s2311119/portable-game/portable-game-console/portable-game-console.ino

// main.ino
#include <SPI.h>
#include <SdFat.h>
#include "LGFX_RP2040_ILI9341.hpp"
#include <LGFX_TFT_eSPI.hpp>  // フォントを使う場合に必要な場合もあります
#include "bmp.h"

#include "pico/stdlib.h"
#include "pico/multicore.h"
#include "pico/time.h"
#include "hardware/gpio.h"

#include "pico/sync.h"
critical_section_t sdLock;

#define LGFX_USE_SD 1
#define H_TRANSPARENT 0xFFFF
#include <malloc.h>
// -------------------------
// 変更が必要なピン設定（回路依存）
// -------------------------
static const int SD_CS_PIN = 22;    // SD カード CS
static const int SD_MISO_PIN = 16;  // SD MISO（プルアップ必須）
static const int SD_SCK_PIN  = 18;
static const int SD_MOSI_PIN = 19;

static const int DAC_CS_PIN   = 17; // MCP4921 CS
static const int DAC_SCK_PIN  = 9;  // ソフトSPIクロック
static const int DAC_MOSI_PIN = 8;  // ソフトSPI MOSI

// -------------------------
// Map / Game / Graphic 等（省略せずそのまま）
// -------------------------
// ここは質問者が既に持っているゲームロジック部分をそのまま使います。
// （読みやすさのため必要最小限のみ再掲します）
// main.ino

#include <vector>      // std::vector を使うために必要
#include <algorithm>   // std::min, std::max を使うために必要

//-----------------------------
/*
ストライカー系: 39->44->49->{54, 55} ->{{61, 62}, {63, 64}}
ガーディアン系: 40->45->50->{56, 57} ->{{65, 66}, {67. 68}}
クリッパー系: 41->46->51->58 ->{69, 70}
メンダ―系: 42->47->52->59 ->{71, 72}
ジャマー系: 43->48->53->60->{73, 74}
*/
//-----------------------------

// グローバル（core0 から参照するけど SD 操作は core1 のみ）
enum EventType {
  EVENT_NONE,
  EVENT_TREASURE_BOX,
  EVENT_STAIR_UP,
  EVENT_STAIR_DOWN,
  EVENT_AUTOMATON,
  EVENT_INN,     // ★追加
  EVENT_SHOP,    // ★追加
  EVENT_STORAGE,  // ★追加
  EVENT_BOSS_BATTLE
};

enum GameState {
  STATE_GAME,
  STATE_MENU, 
  STATE_BATTLE,
  STATE_EVENT,
  STATE_GAME_OVER
};
#include <malloc.h> // これが必要です

class MemoryMonitor {
private:
  unsigned long lastCheckTime = 0;
  const unsigned long INTERVAL = 10000; // 10秒 (10000ms)

public:
  void update() {
    unsigned long now = millis();
    if (now - lastCheckTime >= INTERVAL) {
      lastCheckTime = now;
      printInfo();
    }
  }

  void printInfo() {
    struct mallinfo m = mallinfo();
    
    // RP2040のRAMは約264KBですが、プログラム領域などを除いた
    // ヒープとして使える領域の統計を表示します。
    
    Serial.println("=== Memory Status (10s) ===");
    Serial.printf("Used (使用中): %d bytes (%.2f KB)\n", m.uordblks, m.uordblks / 1024.0);
    Serial.printf("Free (空き)  : %d bytes (%.2f KB)\n", m.fordblks, m.fordblks / 1024.0);
    
    // メモリ断片化の目安（空きがあるのに大きい確保ができない原因）
    // これが小さいと、大きな連続したメモリ(画像など)が確保できません
    // Serial.printf("Max Free Block: %d bytes\n", m.mxordblk); // (環境によっては0になる場合あり)
    
    Serial.println("===========================");
  }
};

class Map {
public:
  int MAP_WIDTH;
  int MAP_HEIGHT;
  int automatonWhoId;
  int currentFloor = 1;
  // マップの寸法（コンストラクタで決定）  
  static const int TILE_SIZE = 32;
  static const int TILE_GRASS = 0;
  static const int TILE_WALL  = 1;
  static const int TILE_STAIR_UP = 2;
  static const int TILE_STAIR_DOWN = 3;
  static const int TILE_BOX_CLOSE = 4;
  static const int TILE_BOX_OPEN = 5;
  static const int TILE_AUTOMATON = 6;
  static const int TILE_INN = 7;     // 宿屋
  static const int TILE_SHOP = 8;    // 店
  static const int TILE_STORAGE = 9; // 預かり所
  static const int TILE_BOSS = 99;//ボス
  // マップデータを保持する動的配列
  std::vector<uint8_t> mapData;

  enum MapType {
    TYPE_MAZE,
    TYPE_DUNGEON,
    TYPE_TOWN,
    TYPE_BOSS_ROOM
  };
  MapType currentType;
  bool isTown = false;
  // ★★★ 追加：部屋の矩形情報を保存する構造体 ★★★
  struct Room {
    int x, y, w, h;
  };

  struct ObjectPos {
    int x, y;
  };

  std::vector<ObjectPos> boxPositions; // 宝箱の位置リスト
  ObjectPos stairUpPos = {-1, -1};    // 上り階段の位置
  ObjectPos stairDownPos = {-1, -1};  // 下り階段の位置
  ObjectPos playerStartPos; //主人公の初期位置

  // ★★★ 修正後のコンストラクタ ★★★
  Map(int max_w, int max_h, MapType type)
  {
    // 初期化リスト (:) ではなく、ここで代入する
    currentType = type;
    /*MAP_WIDTH = ((type != TYPE_MAZE && type != TYPE_DUNGEON) ? random(4, max_w / 2) * 2 + 1 : random(15, max_w / 2) * 2 + 1);
    MAP_HEIGHT = ((type != TYPE_MAZE && type != TYPE_DUNGEON) ? random(4, max_h / 2) * 2 + 1 : random(15, max_h / 2) * 2 + 1);*/
    if (type == TYPE_TOWN) {
      // 集落: 床5x5 + 周囲の壁2 = 7x7
      MAP_WIDTH = 8;
      MAP_HEIGHT = 8;
    } 
    else if (type == TYPE_BOSS_ROOM) {
      // ボス部屋: 床7x7 + 周囲の壁2 = 9x9
      MAP_WIDTH = 9;
      MAP_HEIGHT = 9;
    }
    else {
      // ダンジョン: ランダム (奇数になるように調整)
      // ※ max_w/h が渡されていますが、最低サイズを下回らないように注意
      MAP_WIDTH = random(15, max_w / 2) * 2 + 1;
      MAP_HEIGHT = random(15, max_h / 2) * 2 + 1;
    }
    mapData.assign(MAP_WIDTH * MAP_HEIGHT, TILE_WALL);
    generateMazeAndRooms(type);
    placeObjects();
  }
  int getMAP_WIDTH(){
    return MAP_WIDTH;
  }
  int getMAP_HEIGHT(){
    return MAP_HEIGHT;
  }
  void regenerate(int max_w, int max_h, MapType type){
    // public側のMAP_WIDTH/HEIGHTを変更する
    currentType = type;
    
    isTown = false;
    if (type == TYPE_TOWN) {
      // 集落: 床5x5 + 周囲の壁2 = 7x7
      MAP_WIDTH = 8;
      MAP_HEIGHT = 8;
      isTown = true;
    } 
    else if (type == TYPE_BOSS_ROOM) {
      // ボス部屋: 床7x7 + 周囲の壁2 = 9x9
      MAP_WIDTH = 9;
      MAP_HEIGHT = 9;
    }
    else {
      // ダンジョン: ランダム (奇数になるように調整)
      // ※ max_w/h が渡されていますが、最低サイズを下回らないように注意
      MAP_WIDTH = random(15, max_w / 2) * 2 + 1;
      MAP_HEIGHT = random(15, max_h / 2) * 2 + 1;
    }
    mapData.assign(MAP_WIDTH * MAP_HEIGHT, TILE_WALL);
    if (type == TYPE_BOSS_ROOM) {
      // --- ボス部屋の描画 ---
      
      // 全体を床にする
      for (int i = 0; i < MAP_WIDTH * MAP_HEIGHT; i++) mapData[i] = TILE_GRASS;
      
      // 周囲を壁にする
      for (int x = 0; x < MAP_WIDTH; x++) { 
          mapData[x] = TILE_WALL; 
          mapData[(MAP_HEIGHT-1)*MAP_WIDTH + x] = TILE_WALL; 
      }
      for (int y = 0; y < MAP_HEIGHT; y++) { 
          mapData[y*MAP_WIDTH] = TILE_WALL; 
          mapData[y*MAP_WIDTH + (MAP_WIDTH-1)] = TILE_WALL; 
      }

      // 下り階段 (入り口)
      // 座標が範囲外にならないよう中央下付近に固定
      int stairX = MAP_WIDTH / 2;
      int stairY = MAP_HEIGHT - 3;
      mapData[stairY * MAP_WIDTH + stairX] = TILE_STAIR_DOWN;
      
      // プレイヤー開始位置
      playerStartPos = {stairX, stairY};

      // ★ボス配置 (部屋の中央奥)
      int bossX = MAP_WIDTH / 2;
      int bossY = 5;
      mapData[bossY * MAP_WIDTH + bossX] = TILE_BOSS;

      return; // ボス部屋生成完了
    }
    // メンバー変数を再利用して再生成
    generateMazeAndRooms(type);
    placeObjects();
  }
private:
  //int MAP_WIDTH;
  //int MAP_HEIGHT;
  std::vector<int> pathX, pathY;
  std::vector<int> dirs;
  std::vector<Room> placedRooms;
  std::vector<ObjectPos> grassTiles;
  void generateMazeAndRooms(MapType type) {
    if (type == TYPE_TOWN) {
      // 1. 全体を壁で初期化 (コンストラクタ等で既にされているが念のため)
      // mapData.assign(MAP_WIDTH * MAP_HEIGHT, TILE_WALL); 

      // 2. 中央に大きな広場(草)を作る
      int margin = 2; 
      // マップが小さすぎる場合の保護
      if (MAP_WIDTH <= margin * 2 || MAP_HEIGHT <= margin * 2) margin = 1;

      for(int y = margin; y < MAP_HEIGHT - margin; y++) {
        for(int x = margin; x < MAP_WIDTH - margin; x++) {
          mapData[y * MAP_WIDTH + x] = TILE_GRASS;
        }
      }
      // 集落生成はこれで終わり（階段などは placeObjects で）
      return; 
    }
    if (currentFloor >= 21 && random(100) < 5) { // 例: 5%の確率
      automatonWhoId = 75;
    } 
    else {
      // 通常の仲間
      const int basicAllies[] = {39, 40, 41, 42, 43};
      automatonWhoId = basicAllies[random(5)];
    }
    // --- 1. 穴掘り法 ---
    int startX = 1, startY = 1;
    
    // ★ メンバー変数をクリアして再利用 (new しない)
    pathX.clear(); pathY.clear();
    pathX.reserve(MAP_WIDTH * MAP_HEIGHT / 4);
    pathY.reserve(MAP_WIDTH * MAP_HEIGHT / 4);
    
    pathX.push_back(startX); pathY.push_back(startY);
    mapData[startY * MAP_WIDTH + startX] = TILE_GRASS;
    int dx[]={0,2,0,-2}, dy[]={-2,0,2,0};

    while(!pathX.empty()){
      int cx=pathX.back(), cy=pathY.back();
      
      dirs.clear(); // ★ メンバー変数を再利用
      dirs.reserve(4);
      
      for(int i=0;i<4;i++){
        int nx=cx+dx[i], ny=cy+dy[i];
        if(nx>0 && nx<MAP_WIDTH-1 && ny>0 && ny<MAP_HEIGHT-1 && mapData[ny * MAP_WIDTH + nx]==TILE_WALL) dirs.push_back(i);
      }
      if(!dirs.empty()){
        int dir = dirs[random((int)dirs.size())];
        int wallX = cx + dx[dir]/2, wallY = cy + dy[dir]/2;
        int nextX = cx + dx[dir], nextY = cy + dy[dir];
        mapData[wallY * MAP_WIDTH + wallX] = TILE_GRASS;
        mapData[nextY * MAP_WIDTH + nextX] = TILE_GRASS;
        pathX.push_back(nextX); pathY.push_back(nextY);
      } else {
        pathX.pop_back(); pathY.pop_back();
      }
    }

    // --- 2. rooms ---
    if(type == TYPE_DUNGEON) {
      int numRooms = random(0, 3);
      int minRoomSize = 3;
      int maxRoomSize = 8;

      placedRooms.clear(); // ★ メンバー変数を再利用
      placedRooms.reserve(numRooms);

      int maxAttempts = 100;

      for (int i = 0; i < numRooms; i++) {
        bool roomPlaced = false;
        for (int attempt = 0; attempt < maxAttempts; attempt++) {
          int w = random(minRoomSize, maxRoomSize + 1);
          int h = random(minRoomSize, maxRoomSize + 1);
          int x = random(1, MAP_WIDTH - w - 2);
          int y = random(1, MAP_HEIGHT - h - 2);
          Room newRoom = {x, y, w, h};
          bool overlaps = false;
          for (const auto& existingRoom : placedRooms) {
            if (newRoom.x < existingRoom.x + existingRoom.w &&
                newRoom.x + newRoom.w > existingRoom.x &&
                newRoom.y < existingRoom.y + existingRoom.h &&
                newRoom.y + newRoom.h > existingRoom.y) {
              overlaps = true; break;
            }
          }
          if (!overlaps) {
            carveRoom(newRoom.x, newRoom.y, newRoom.x + newRoom.w, newRoom.y + newRoom.h);
            placedRooms.push_back(newRoom);
            roomPlaced = true;
            break;
          }
        }
      }
    }
  }

  // (generateDungeon のヘルパー関数) 部屋を掘る
  void carveRoom(int x1, int y1, int x2, int y2) {
    for (int y = y1; y < y2; y++) {
      for (int x = x1; x < x2; x++) {
        if (x > 0 && x < MAP_WIDTH - 1 && y > 0 && y < MAP_HEIGHT - 1) {
          mapData[y * MAP_WIDTH + x] = TILE_GRASS;
        }
      }
    }
  }

  void placeObjects() {
    boxPositions.clear();
    stairUpPos = {-1, -1};
    stairDownPos = {-1, -1};
    playerStartPos = {1, 1};

    grassTiles.clear(); // ★ メンバー変数を再利用
    grassTiles.reserve((MAP_WIDTH-2) * (MAP_HEIGHT-2) / 2);
    for (int y = 1; y < MAP_HEIGHT - 1; ++y) {
      for (int x = 1; x < MAP_WIDTH - 1; ++x) {
        if (mapData[y * MAP_WIDTH + x] == TILE_GRASS) grassTiles.push_back({x,y});
      }
    }
    if (grassTiles.empty()) return;
    int idx;
    
    if (currentType == TYPE_TOWN) {
      // 1. 上り階段
      idx = random((int)grassTiles.size());
      stairUpPos = grassTiles[idx];
      mapData[stairUpPos.y * MAP_WIDTH + stairUpPos.x] = TILE_STAIR_UP;
      grassTiles[idx] = grassTiles.back(); grassTiles.pop_back();

      // 2. 下り階段 (1階以外)
      if (currentFloor > 1 && !grassTiles.empty()) {
        idx = random((int)grassTiles.size());
        stairDownPos = grassTiles[idx];
        mapData[stairDownPos.y * MAP_WIDTH + stairDownPos.x] = TILE_STAIR_DOWN;
        grassTiles[idx] = grassTiles.back(); grassTiles.pop_back();
      }
      if (currentFloor > 1){
        playerStartPos = stairDownPos;
      }else{
        playerStartPos = grassTiles[random((int)grassTiles.size())];
      }
      // ★★★ 3. 施設の配置 ★★★
      if (!grassTiles.empty()) { // 宿屋
        idx = random((int)grassTiles.size());
        ObjectPos pos = grassTiles[idx];
        mapData[pos.y * MAP_WIDTH + pos.x] = TILE_INN;
        grassTiles[idx] = grassTiles.back(); grassTiles.pop_back();
      }
      if (!grassTiles.empty()) { // 店
        idx = random((int)grassTiles.size());
        ObjectPos pos = grassTiles[idx];
        mapData[pos.y * MAP_WIDTH + pos.x] = TILE_SHOP;
        grassTiles[idx] = grassTiles.back(); grassTiles.pop_back();
      }
      if (!grassTiles.empty()) { // 預かり所
        idx = random((int)grassTiles.size());
        ObjectPos pos = grassTiles[idx];
        mapData[pos.y * MAP_WIDTH + pos.x] = TILE_STORAGE;
        grassTiles[idx] = grassTiles.back(); grassTiles.pop_back();
      }  
      return; 
    }

    // pick using swap-pop to avoid erase shift
    idx = random((int)grassTiles.size());
    stairDownPos = grassTiles[idx];
    playerStartPos = stairDownPos;
    mapData[stairDownPos.y * MAP_WIDTH + stairDownPos.x] = TILE_STAIR_DOWN;
    grassTiles[idx] = grassTiles.back();
    grassTiles.pop_back();

    idx = random((int)grassTiles.size());
    stairUpPos = grassTiles[idx];
    mapData[stairUpPos.y * MAP_WIDTH + stairUpPos.x] = TILE_STAIR_UP;
    grassTiles[idx] = grassTiles.back();
    grassTiles.pop_back();

    if (!grassTiles.empty()) {
      idx = random((int)grassTiles.size());
      ObjectPos allyPos = grassTiles[idx];
      // ★ TODO: 今は 39 で固定。将来的にはフロア番号で who ID を変える
      // (mapData は who ID を保持できないので、別の変数に持つ)
      mapData[allyPos.y * MAP_WIDTH + allyPos.x] = TILE_AUTOMATON; 
      grassTiles[idx] = grassTiles.back();
      grassTiles.pop_back();
    }

    int maxBoxes = std::max(0, (int)grassTiles.size() / 5);
    int numBoxes = 0;
    if (maxBoxes > 0) numBoxes = random(1, std::min(maxBoxes, 10) + 1);
    for (int i = 0; i < numBoxes; ++i) {
      if (grassTiles.empty()) break;
      int j = random((int)grassTiles.size());
      ObjectPos boxPos = grassTiles[j];
      mapData[boxPos.y * MAP_WIDTH + boxPos.x] = TILE_BOX_CLOSE;
      boxPositions.push_back(boxPos);
      grassTiles[j] = grassTiles.back();
      grassTiles.pop_back();
    }
  }

  // ★★★ 追加: 迷路生成後に宝箱と階段を配置する関数 ★★★
  
};

class Item {
public:
  enum ItemType {
    ITEM_CONSUMABLE, // 消費アイテム (回復薬など)
    ITEM_WEAPON,     // 武器
    ITEM_ARMOR,      // 防具
    ITEM_ACCESSORY,  // アクセサリー
    ITEM_MATERIAL,   // 素材 (換金用)
    ITEM_IMPORTANT   // 大事なもの
  };
  ItemType type; // ★ 追加: 種類
  int value;     // ★ 追加: 威力 (武器ならATK、防具ならDEF、薬なら回復量)
  int price;     // ★ 追加: 買値 (売値はこの半額にするのが一般的)
  int id;
  const char* name;

  // コンストラクタ
  Item(int _id = 0, const char* _name = "", ItemType _type = ITEM_MATERIAL, int _value = 0, int _price = 0) {
    id = _id;
    name = _name;
    type = _type;
    value = _value;
    price = _price;
  }
};

class Skill {
public:
  int id;
  const char* name;
  int tpCost; // ★消費TP (ゼンマイ)
  int power;  // ★技の威力 (Senseステータスで計算)
  enum class StatDependence {
    NONE, // 依存なし (固定値など)
    ATK,  // 物理 (Attack vs Defense)
    SEN   // 魔法/技術 (Sense vs Sense)
  };
  // main.ino (Skill クラスのコンストラクタ 322行目あたり)

  enum class EffectType {
    NONE,             // 効果なし
    DAMAGE,           // 物理・属性ダメージ (powerを参照)
    HEAL,             // HP回復 (powerを参照)
    CURE_STATUS,      // 状態異常の治療 (例: キュア)
    BUFF,             // 強化 (例: パワーチャージ, クイックステップ)
    DEBUFF,           // 弱体化 (例: スロウ, パワーダウン)
    REVIVE,           // 蘇生 (例: リザレクション)
    MULTI_HIT_DAMAGE, // 多段ヒット (例: ツインエッジ)
    SPECIAL           // その他 (例: 逃走, 仲間を呼ぶ, 複合効果など)
  };

  // スキルの「対象範囲」
  enum class TargetScope {
    SELF,             // 使用者自身
    SINGLE_ALLY,      // 味方単体
    SINGLE_ENEMY,     // 敵単体
    ALL_ALLIES,       // 味方全体
    ALL_ENEMIES,      // 敵全体
    RANDOM_ENEMY      // 敵ランダム (複数回ヒット用など)
  };
  EffectType type;      // スキルの効果タイプ
  TargetScope scope;    // スキルの対象範囲
  StatDependence dependence;
  enum class Category {
    PHYSICAL, // 物理
    MELODY,   // 旋律 (魔法)
    OTHER     // その他 (バフなど)
  };
  Category category;

  Skill(int recid) {
    id = recid;

    // デフォルト値
    name = "？？？";
    tpCost = 0;
    power = 0;

    type = EffectType::DAMAGE;
    scope = TargetScope::SINGLE_ENEMY;
    dependence = StatDependence::ATK;
    category = Category::PHYSICAL;

    switch (id) {
      // --- 主人公 (ID 0-19) ---
      case 0: name = "プチノイズ"; tpCost = 5; power = 10; dependence = StatDependence::SEN; break; // 魔法っぽいのでSEN
      case 1: name = "ノイズ・ブラスト"; tpCost = 3; power = 60; dependence = StatDependence::SEN; break;
      case 2: name = "レゾナンス・ウェイブ"; tpCost = 6; power = 40; scope = TargetScope::ALL_ENEMIES; dependence = StatDependence::SEN; break;
      case 3: name = "ディソナンス"; tpCost = 14; power = 120; dependence = StatDependence::SEN; break;
      // (回復・補助系は dependence はあまり関係ないが、回復量はSEN依存にするのが一般的)
      case 4: name = "ファースト・エイド"; tpCost = 8; power = 40; type = EffectType::HEAL; scope = TargetScope::SINGLE_ALLY; dependence = StatDependence::SEN; break;
      case 5: name = "ピュリファイ"; tpCost = 10; power = 0; type = EffectType::CURE_STATUS; scope = TargetScope::SINGLE_ALLY; break;
      case 6: name = "ヒーリング・サークル"; tpCost = 20; power = 80; type = EffectType::HEAL; scope = TargetScope::ALL_ALLIES; dependence = StatDependence::SEN; break;
      case 7: 
        name = "チューニング・アタック"; tpCost = 5; power = 0; 
        type = EffectType::BUFF; scope = TargetScope::SINGLE_ALLY; 
        break; // 味方単体ATKアップ
      case 8: 
        name = "チューニング・ガード"; tpCost = 5; power = 0; 
        type = EffectType::BUFF; scope = TargetScope::SINGLE_ALLY; 
        break; // 味方単体DEFアップ
      case 9: 
        name = "アレグロ"; tpCost = 10; power = 0; 
        type = EffectType::BUFF; scope = TargetScope::ALL_ALLIES; 
        break; // 味方全体SPDアップ
      case 10: 
        name = "ラレンタンド"; tpCost = 5; power = 0; 
        type = EffectType::DEBUFF; scope = TargetScope::SINGLE_ENEMY; 
        break; // 敵単体SPDダウン
      case 11: 
        name = "ノイズ・ジャミング"; tpCost = 10; power = 0; 
        type = EffectType::DEBUFF; scope = TargetScope::ALL_ENEMIES; 
        break; // 敵全体ATKダウン
      // (バフ・デバフ系は威力0なので省略、奥義はSEN)
      case 12: name = "グランド・シンフォニー"; tpCost = 60; power = 300; scope = TargetScope::ALL_ENEMIES; dependence = StatDependence::SEN; break;
      case 13: name = "完全調律"; tpCost = 60; power = 999; type = EffectType::HEAL; scope = TargetScope::ALL_ALLIES; dependence = StatDependence::SEN; break;
      // --- ストライカー (who=39) ---
      case 20: 
        name = "ハードヒット"; tpCost = 5; power = 80; 
        type = EffectType::DAMAGE; scope = TargetScope::SINGLE_ENEMY; 
        break;
      case 21: 
        name = "パワーチャージ"; tpCost = 8; power = 0; 
        type = EffectType::BUFF; scope = TargetScope::SELF; 
        break; // (ATK 1.5倍バフなど)

      // --- ギア・ソルジャー (who=40) ---
      case 22: 
        name = "スラッシュ"; tpCost = 8; power = 150; 
        type = EffectType::DAMAGE; scope = TargetScope::SINGLE_ENEMY; 
        break;
      case 23: 
        name = "ダブルヒット"; tpCost = 10; power = 100; 
        type = EffectType::MULTI_HIT_DAMAGE; scope = TargetScope::SINGLE_ENEMY; 
        break; // (30ダメージ x 2回)

      // --- ギア・ナイト (who=41) ---
      case 24: 
        name = "アーマーブレイク"; tpCost = 10; power = 150; 
        type = EffectType::SPECIAL; scope = TargetScope::SINGLE_ENEMY; 
        break; // (防御無視 or 防御ダウン)
      case 25: 
        name = "ソードダンス"; tpCost = 5; power = 0; 
        type = EffectType::BUFF; scope = TargetScope::SELF; 
        break; // (ATK/SPD バフ)

      // --- ヴァンガード (who=42) ---
      case 26: 
        name = "シールドスマッシュ"; tpCost = 20; power = 300; 
        type = EffectType::DAMAGE; scope = TargetScope::SINGLE_ENEMY; 
        break;
      case 27: 
        name = "かばう"; tpCost = 5; power = 0; 
        type = EffectType::SPECIAL; scope = TargetScope::SELF; 
        break; // (仲間を守る)

      // --- スワッシュバックラー (who=45) ---
      case 28: 
        name = "ファントムエッジ"; tpCost = 10; power = 200; 
        type = EffectType::DAMAGE; scope = TargetScope::SINGLE_ENEMY; 
        break; // (クリティカル率 高)
      case 29: 
        name = "トリックステップ"; tpCost = 5; power = 0; 
        type = EffectType::BUFF; scope = TargetScope::SELF; 
        break; // (SPD/LCK バフ)
      
      // --- オーバーロード (who=43) ---
      case 30: 
        name = "ギガブレイク"; tpCost = 40; power = 400; 
        type = EffectType::DAMAGE; scope = TargetScope::SINGLE_ENEMY; 
        break;
      case 31: 
        name = "王者の波動"; tpCost = 10; power = 0; 
        type = EffectType::BUFF; scope = TargetScope::ALL_ALLIES; 
        break; // (味方全体 ATK/DEF バフ)
      case 32: 
        name = "キングス・シールド"; tpCost = 10; power = 0; 
        type = EffectType::SPECIAL; scope = TargetScope::SELF; 
        break; // (物理・旋律反射)
      case 33: 
        name = "デッドエンド"; tpCost = 60; power = 600; 
        type = EffectType::DAMAGE; scope = TargetScope::SINGLE_ENEMY; 
        break;

      // --- デストロイヤー (who=44) ---
      case 34: 
        name = "バーサーク"; tpCost = 3; power = 0; 
        type = EffectType::BUFF; scope = TargetScope::SELF; 
        break; // (ATK 2倍 / DEF 0.5倍)
      case 35: 
        name = "カラミティ・エンド"; tpCost = 10; power = 200; 
        type = EffectType::DAMAGE; scope = TargetScope::SINGLE_ENEMY; 
        break; // (HPが低いほど高威力)
      case 36: 
        name = "トリプルスラッシュ"; tpCost = 15; power = 150; 
        type = EffectType::MULTI_HIT_DAMAGE; scope = TargetScope::SINGLE_ENEMY; 
        break; // (80ダメージ x 3回)
      case 37: 
        name = "デモリッシュ"; tpCost = 55; power = 600;
        type = EffectType::DAMAGE; scope = TargetScope::SINGLE_ENEMY; 
        break;

      // --- ゼロ・ブレード (who=46) ---
      case 38: 
        name = "ソニックブレイド"; tpCost = 10; power = 100; 
        type = EffectType::DAMAGE; scope = TargetScope::SINGLE_ENEMY; 
        break; // (必ず先制)
      case 39: 
        name = "ミラーズエッジ"; tpCost = 5; power = 0; 
        type = EffectType::BUFF; scope = TargetScope::SELF; 
        break; // (回避率 2倍バフ)
      case 40: 
        name = "刹那"; tpCost = 20; power = 400; 
        type = EffectType::DAMAGE; scope = TargetScope::SINGLE_ENEMY; 
        break; // (高クリティカル率)
      case 41: 
        name = "無空"; tpCost = 65; power = 1000; 
        type = EffectType::DAMAGE; scope = TargetScope::SINGLE_ENEMY; 
        break; // (TP消費が激しい)

      // --- ヴォイド・ストーカー (who=47) ---
      case 42: 
        name = "アサシネイト"; tpCost = 10; power = 300; 
        type = EffectType::SPECIAL; scope = TargetScope::SINGLE_ENEMY; 
        break; // (確率で即死)
      case 43: 
        name = "ダーククローク"; tpCost = 3; power = 0; 
        type = EffectType::BUFF; scope = TargetScope::SELF; 
        break; // (姿を消す / 狙われない)
      case 44: 
        name = "ペインサイクル"; tpCost = 10; power = 300; 
        type = EffectType::SPECIAL; scope = TargetScope::SINGLE_ENEMY; 
        break; // (与ダメージ分 HP 回復)
      case 45: 
        name = "ヴォイド・ショック"; tpCost = 45; power = 500; 
        type = EffectType::SPECIAL; scope = TargetScope::SINGLE_ENEMY; 
        break; // (高確率で状態異常)

      // --- ガーディアン (who=1) ---
      case 46: 
        name = "プロテクト"; tpCost = 5; power = 0; 
        type = EffectType::BUFF; scope = TargetScope::SINGLE_ALLY; 
        break; // (味方単体 DEF 1.5倍)
      case 47: 
        name = "シールドバッシュ"; tpCost = 10; power = 80; 
        type = EffectType::SPECIAL; scope = TargetScope::SINGLE_ENEMY; 
        break; // (威力20 + 確率でスタン)

      // --- フォートレス (who=6) ---
      case 48: 
        name = "ウォール"; tpCost = 10; power = 0; 
        type = EffectType::BUFF; scope = TargetScope::ALL_ALLIES; 
        break; // (味方全体 DEF 1.2倍)
      case 49: 
        name = "挑発"; tpCost = 10; power = 0; 
        type = EffectType::SPECIAL; scope = TargetScope::SELF; 
        break; // (敵の攻撃を自分に集める)

      // --- キャッスル・ウォール (who=11) ---
      case 50: 
        name = "リフレクト"; tpCost = 5; power = 0; 
        type = EffectType::BUFF; scope = TargetScope::SELF; 
        break; // (物理攻撃を一度だけ反射)
      case 51: 
        name = "ガーディアン魂"; tpCost = 5; power = 0; 
        type = EffectType::BUFF; scope = TargetScope::SELF; 
        break; // (DEF 2倍、SPD 0.5倍)

      // --- バスティオン (who=17) ---
      case 52: 
        name = "鉄壁"; tpCost = 10; power = 0; 
        type = EffectType::BUFF; scope = TargetScope::SELF; 
        break; // (3ターン DEF 2.5倍)
      case 53: 
        name = "カウンター"; tpCost = 5; power = 100; 
        type = EffectType::SPECIAL; scope = TargetScope::SELF; 
        break; // (受けたダメージを反撃)

      // --- イージス (who=18) ---
      case 54: 
        name = "リペア"; tpCost = 5; power = 60; 
        type = EffectType::HEAL; scope = TargetScope::SINGLE_ALLY; 
        break; // (味方単体 回復)
      case 55: 
        name = "フォースフィールド"; tpCost = 10; power = 0; 
        type = EffectType::BUFF; scope = TargetScope::SINGLE_ALLY; 
        break; // (味方単体 ダメージ無効 1回)

      // --- アダマンタイト (who=26) ---
      case 56: 
        name = "アダマン・ボディ"; tpCost = 20; power = 0; 
        type = EffectType::BUFF; scope = TargetScope::SELF; 
        break; // (物理ダメージを 1 に)
      case 57: 
        name = "自己修復"; tpCost = 0; power = 0; 
        type = EffectType::BUFF; scope = TargetScope::SELF; 
        break; // (HPリジェネ(大))
      case 58: 
        name = "ラストスタンド"; tpCost = 10; power = 0; 
        type = EffectType::BUFF; scope = TargetScope::SELF; 
        break; // (HP1で耐える)
      case 59: 
        name = "ギガンティック・ウォール"; tpCost = 20; power = 0; 
        type = EffectType::BUFF; scope = TargetScope::ALL_ALLIES; 
        break; // (味方全体 DEF 2倍)

      // --- インヴィンシブル (who=27) ---
      case 60: 
        name = "超回復"; tpCost = 0; power = 500; 
        type = EffectType::HEAL; scope = TargetScope::SINGLE_ALLY; 
        break; // (HP大回復)
      case 61: 
        name = "オートリバイブ"; tpCost = 0; power = 0; 
        type = EffectType::BUFF; scope = TargetScope::SELF; 
        break; // (自動蘇生 1回)
      case 62: 
        name = "最大HP上昇"; tpCost = 0; power = 0; 
        type = EffectType::BUFF; scope = TargetScope::SELF; 
        break; // (戦闘中 MaxHP 1.5倍)
      case 63: 
        name = "無敵"; tpCost = 5; power = 0; 
        type = EffectType::BUFF; scope = TargetScope::SELF; 
        break; // (1ターン ダメージ 0)

      // --- ディヴァイン・シールド (who=28) ---
      case 64: 
        name = "全体バリア"; tpCost = 15; power = 0; 
        type = EffectType::BUFF; scope = TargetScope::ALL_ALLIES; 
        break; // (味方全体 ダメージ無効 1回)
      case 65: 
        name = "旋律反射"; tpCost = 5; power = 0; 
        type = EffectType::BUFF; scope = TargetScope::SELF; 
        break; // (旋律(魔法)反射)
      case 66: 
        name = "キュア・オール"; tpCost = 20; power = 0; 
        type = EffectType::CURE_STATUS; scope = TargetScope::ALL_ALLIES; 
        break; // (味方全体 状態異常回復)
      case 67: 
        name = "ディバイン・ウォール"; tpCost = 20; power = 0;
        type = EffectType::BUFF; scope = TargetScope::ALL_ALLIES; 
        break; // (効果: 全ダメージ軽減)
      
      // --- リジェネレーター (who=29) ---
      case 68: 
        name = "全体リペア"; tpCost = 10; power = 1000; 
        type = EffectType::HEAL; scope = TargetScope::ALL_ALLIES; 
        break; // (味方全体 回復)
      case 69: 
        name = "リザレクション"; tpCost = 0; power = 0; 
        type = EffectType::REVIVE; scope = TargetScope::SINGLE_ALLY; 
        break; // (味方単体 蘇生)
      case 70: 
        name = "TPリジェネ"; tpCost = 0; power = 0; 
        type = EffectType::BUFF; scope = TargetScope::SELF; 
        break; // (自身のTPを徐々に回復)
      case 71: 
        name = "フル・キュア"; tpCost = 10; power = 9999; 
        type = EffectType::HEAL; scope = TargetScope::ALL_ALLIES; 
        break; // (味方全体 HP全回復)

      // --- クリッパー (who=41) ---
      case 72: 
        name = "カッティング"; tpCost = 7; power = 80; 
        type = EffectType::DAMAGE; scope = TargetScope::SINGLE_ENEMY; 
        break;
      case 73: 
        name = "クイックステップ"; tpCost = 5; power = 0; 
        type = EffectType::BUFF; scope = TargetScope::SELF; 
        break; // (自身 SPD バフ)

      // --- ブレード・ダンサー (who=46) ---
      case 74: 
        name = "ツインエッジ"; tpCost = 10; power = 60; 
        type = EffectType::MULTI_HIT_DAMAGE; scope = TargetScope::SINGLE_ENEMY; 
        break; // (35ダメージ x 2回)
      case 75: 
        name = "エアリアルダンス"; tpCost = 5; power = 0; 
        type = EffectType::BUFF; scope = TargetScope::SELF; 
        break; // (自身 AGI バフ)

      // --- サイクロン・ダンサー (who=51) ---
      case 76: 
        name = "スパイラルエッジ"; tpCost = 15; power = 100; 
        type = EffectType::MULTI_HIT_DAMAGE; scope = TargetScope::SINGLE_ENEMY; 
        break; // (70ダメージ x 2回)
      case 77: 
        name = "エアステップ"; tpCost = 5; power = 0; 
        type = EffectType::BUFF; scope = TargetScope::SINGLE_ALLY; 
        break; // (味方単体 SPD/AGI バフ)

      // --- テンペスト (who=58) ---
      case 78: 
        name = "ゲイルストライク"; tpCost = 5; power = 140; 
        type = EffectType::DAMAGE; scope = TargetScope::SINGLE_ENEMY; 
        break; // (風属性)
      case 79: 
        name = "ラピッドムーブ"; tpCost = 10; power = 0; 
        type = EffectType::BUFF; scope = TargetScope::ALL_ALLIES; 
        break; // (味方全体 SPD バフ)

      // --- シルフィード (who=69) ---
      case 80: 
        name = "インビジブルエッジ"; tpCost = 10; power = 200; 
        type = EffectType::DAMAGE; scope = TargetScope::SINGLE_ENEMY; 
        break; // (回避無視)
      case 81: 
        name = "ウインドウォール"; tpCost = 20; power = 0; 
        type = EffectType::BUFF; scope = TargetScope::ALL_ALLIES; 
        break; // (味方全体 回避率UP)
      case 82: 
        name = "ストームブリンガー"; tpCost = 10; power = 150; 
        type = EffectType::DAMAGE; scope = TargetScope::ALL_ENEMIES; 
        break; // (全体 風属性攻撃)
      case 83: 
        name = "精霊の舞"; tpCost = 5; power = 0; 
        type = EffectType::BUFF; scope = TargetScope::SELF; 
        break; // (自身のTP徐々に回復)

      // --- アクセラレーター (who=70) ---
      case 84: 
        name = "マッハブレイド"; tpCost = 13; power = 400; 
        type = EffectType::DAMAGE; scope = TargetScope::SINGLE_ENEMY; 
        break; // (必ず先制)
      case 85: 
        name = "オーバークロック"; tpCost = 10; power = 0; 
        type = EffectType::BUFF; scope = TargetScope::SELF; 
        break; // (自身 2回行動)
      case 86: 
        name = "リミットブレイク"; tpCost = 10; power = 0; 
        type = EffectType::BUFF; scope = TargetScope::SELF; 
        break; // (自身のATK/SPD 最大まで上昇)
      case 87: 
        name = "タービュランス"; tpCost = 30; power = 300; 
        type = EffectType::SPECIAL; scope = TargetScope::ALL_ENEMIES; 
        break; // (全体 風属性 + SPDダウン)

      // --- メンダー (who=42) ---
      case 88: 
        name = "リペア"; tpCost = 5; power = 50; 
        type = EffectType::HEAL; scope = TargetScope::SINGLE_ALLY; 
        break; // (単体 HP回復)
      case 89: 
        name = "キュア"; tpCost = 5; power = 0; 
        type = EffectType::CURE_STATUS; scope = TargetScope::SINGLE_ALLY; 
        break; // (単体 状態異常回復)

      // --- (第1進化: who=47) ---
      case 90: 
        name = "リペア・プラス"; tpCost = 10; power = 150; 
        type = EffectType::HEAL; scope = TargetScope::SINGLE_ALLY; 
        break; // (単体 HP回復(中))
      case 91: 
        name = "リフレッシュ"; tpCost = 5; power = 0; 
        type = EffectType::CURE_STATUS; scope = TargetScope::SINGLE_ALLY; 
        break; // (単体 弱体解除)

      // --- (第2進化: who=52) ---
      case 92: 
        name = "エリア・リペア"; tpCost = 15; power = 100; 
        type = EffectType::HEAL; scope = TargetScope::ALL_ALLIES; 
        break; // (全体 HP回復(小))
      case 93: 
        name = "リザレクション"; tpCost = 10; power = 0; 
        type = EffectType::REVIVE; scope = TargetScope::SINGLE_ALLY; 
        break; // (単体 蘇生(HP中))

      // --- (第3進化: who=59) ---
      case 94: 
        name = "フル・リペア"; tpCost = 15; power = 500; 
        type = EffectType::HEAL; scope = TargetScope::SINGLE_ALLY; 
        break; // (単体 HP回復(大))
      case 95: 
        name = "オートリペア"; tpCost = 10; power = 0; 
        type = EffectType::BUFF; scope = TargetScope::SINGLE_ALLY; 
        break; // (単体 HP自動回復)

      // --- (最終進化A: who=71) ---
      case 96: 
        name = "エリア・リペア・プラス"; tpCost = 25; power = 250; 
        type = EffectType::HEAL; scope = TargetScope::ALL_ALLIES; 
        break; // (全体 HP回復(中))
      case 97: 
        name = "リジェネフィールド"; tpCost = 20; power = 0; 
        type = EffectType::BUFF; scope = TargetScope::ALL_ALLIES; 
        break; // (全体 HP自動回復)
      case 98: 
        name = "アセンション"; tpCost = 60; power = 0; 
        type = EffectType::REVIVE; scope = TargetScope::ALL_ALLIES; 
        break; // (全体 蘇生(HP全快))
      case 99: 
        name = "ホーリー・ウォール"; tpCost = 20; power = 0;
        type = EffectType::BUFF; scope = TargetScope::ALL_ALLIES; 
        break; // (全体 状態異常無効 1回)

      // --- (最終進化B: who=72) ---
      case 100: 
        name = "TPチャージ"; tpCost = 10; power = 300; 
        type = EffectType::SPECIAL; scope = TargetScope::SINGLE_ALLY; 
        break; // (単体 TP回復)
      case 101: 
        name = "ディスペル"; tpCost = 5; power = 0; 
        type = EffectType::DEBUFF; scope = TargetScope::SINGLE_ENEMY; 
        break; // (敵単体 強化解除)
      case 102: 
        name = "TPリジェネ"; tpCost = 5; power = 0; 
        type = EffectType::BUFF; scope = TargetScope::SELF; 
        break; // (自身 TP自動回復)
      case 103: 
        name = "オラクルフィールド"; tpCost = 5; power = 0; 
        type = EffectType::BUFF; scope = TargetScope::ALL_ALLIES; 
        break; // (全体 TP徐々に回復)

      // --- ジャマー (who=43) ---
      case 104: 
        name = "スロウ"; tpCost = 5; power = 0; 
        type = EffectType::DEBUFF; scope = TargetScope::SINGLE_ENEMY; 
        break; // (敵単体 SPD ダウン)
      case 105: 
        name = "ポイズン"; tpCost = 5; power = 50; 
        type = EffectType::SPECIAL; scope = TargetScope::SINGLE_ENEMY; 
        break; // (ダメージ + 確率で毒)

      // --- (第1進化: who=48) ---
      case 106: 
        name = "パワーダウン"; tpCost = 5; power = 0; 
        type = EffectType::DEBUFF; scope = TargetScope::SINGLE_ENEMY; 
        break; // (敵単体 ATK ダウン)
      case 107: 
        name = "ガードダウン"; tpCost = 5; power = 0; 
        type = EffectType::DEBUFF; scope = TargetScope::SINGLE_ENEMY; 
        break; // (敵単体 DEF ダウン)

      // --- (第2進化: who=53) ---
      case 108: 
        name = "エリア・スロウ"; tpCost = 10; power = 0; 
        type = EffectType::DEBUFF; scope = TargetScope::ALL_ENEMIES; 
        break; // (敵全体 SPD ダウン)
      case 109: 
        name = "サイレンス"; tpCost = 15; power = 0; 
        type = EffectType::DEBUFF; scope = TargetScope::SINGLE_ENEMY; 
        break; // (敵単体 確率で沈黙)

      // --- (第3進化: who=60) ---
      case 110: 
        name = "デッドリーポイズン"; tpCost = 10; power = 400; 
        type = EffectType::SPECIAL; scope = TargetScope::SINGLE_ENEMY; 
        break; // (ダメージ + 確率で猛毒)
      case 111: 
        name = "TPドレイン"; tpCost = 5; power = 380; 
        type = EffectType::SPECIAL; scope = TargetScope::SINGLE_ENEMY; 
        break; // (敵単体 TP吸収)

      // --- (最終進化A: who=73) ---
      case 112: 
        name = "エリア・ブレイク"; tpCost = 15; power = 0; 
        type = EffectType::DEBUFF; scope = TargetScope::ALL_ENEMIES; 
        break; // (敵全体 ATK/DEF ダウン)
      case 113: 
        name = "カオスフィールド"; tpCost = 20; power = 0; 
        type = EffectType::DEBUFF; scope = TargetScope::ALL_ENEMIES; 
        break; // (敵全体 確率で混乱)
      case 114: 
        name = "ディザスター"; tpCost = 30; power = 1500; 
        type = EffectType::SPECIAL; scope = TargetScope::SINGLE_ENEMY; 
        break; // (無属性 + 全状態異常付与)
      case 115: 
        name = "ペイン・イーター"; tpCost = 30; power = 1000; 
        type = EffectType::DAMAGE; scope = TargetScope::SINGLE_ENEMY; 
        break; // (状態異常の敵に特効)

      // --- (最終進化B: who=74) ---
      case 116: 
        name = "ロックダウン"; tpCost = 0; power = 0; 
        type = EffectType::DEBUFF; scope = TargetScope::SINGLE_ENEMY; 
        break; // (敵単体 確率で行動不能)
      case 117: 
        name = "バニッシュ"; tpCost = 5; power = 0; 
        type = EffectType::DEBUFF; scope = TargetScope::SINGLE_ENEMY; 
        break; // (敵単体 強化全解除)
      case 118: 
        name = "ワールド・ダウン"; tpCost = 15; power = 0; 
        type = EffectType::DEBUFF; scope = TargetScope::ALL_ENEMIES; 
        break; // (敵全体 全能力ダウン)
      case 119: 
        name = "エナジー・バーン"; tpCost = 50; power = 300; 
        type = EffectType::DAMAGE; scope = TargetScope::SINGLE_ENEMY; 
        break; // (敵のTPが多いほど高威力)

      // --- はぐれノイズ (仲間用) (who=75) ---
      case 120: 
        name = "ノイズヒット"; tpCost = 0; power = 90; 
        type = EffectType::DAMAGE; scope = TargetScope::SINGLE_ENEMY; 
        break; // (シンプルな攻撃)
      case 121: 
        name = "ソニックダガー"; tpCost = 0; power = 120; 
        type = EffectType::DAMAGE; scope = TargetScope::SINGLE_ENEMY; 
        break; // (必ず先制攻撃)
      case 122: 
        name = "かく乱"; tpCost = 0; power = 0; 
        type = EffectType::DEBUFF; scope = TargetScope::SINGLE_ENEMY; 
        break; // (攻撃 + 確率で混乱)
      case 123: 
        name = "ファントムラッシュ"; tpCost = 0; power = 130; 
        type = EffectType::MULTI_HIT_DAMAGE; scope = TargetScope::RANDOM_ENEMY; 
        break; // (40ダメージ x 2-4回ランダム攻撃)

      // --- はぐれキング (仲間用) (who=76) ---
      case 124: 
        name = "キングスピア"; tpCost = 0; power = 200; 
        type = EffectType::DAMAGE; scope = TargetScope::SINGLE_ENEMY; 
        break; // (防御無視攻撃)
      case 125: 
        name = "ノイズストーム"; tpCost = 0; power = 150; 
        type = EffectType::DAMAGE; scope = TargetScope::ALL_ENEMIES; 
        break; // (敵全体攻撃)
      case 126: 
        name = "ロイヤルチャージ"; tpCost = 0; power = 1000; 
        type = EffectType::DAMAGE; scope = TargetScope::SINGLE_ENEMY; 
        break; // (高威力だが次のターン行動不可)
      case 127: 
        name = "ラッキーセブン"; tpCost = 0; power = 777; 
        type = EffectType::MULTI_HIT_DAMAGE; scope = TargetScope::RANDOM_ENEMY; 
        break; // (77ダメージ x 1-7回ランダム攻撃)

      default:
        name = "？？？";
        tpCost = 0;
        power = 0;
        type = EffectType::NONE; scope = TargetScope::SINGLE_ENEMY; 
        break;
    }
    // メンダー系 (88-103) は全て Sense 依存
    if (id >= 88 && id <= 103) {
        dependence = StatDependence::SEN;
    }
    // ジャマー系 (104-119) も全て Sense 依存
    if (id >= 104 && id <= 119) {
        dependence = StatDependence::SEN;
    }
    // 主人公の攻撃スキル (1-3, 12)
    if (id <= 3 || id == 12) {
        dependence = StatDependence::SEN;
    }
    // はぐれ系 (125 ノイズストーム, 126 ロイヤルチャージ) は魔法っぽい？
    if (id == 125 || id == 126) {
        dependence = StatDependence::SEN;
    }
    // スキル設定がすべて確定した後にカテゴリを決定
    bool isOffensive =
        type == EffectType::DAMAGE ||
        type == EffectType::MULTI_HIT_DAMAGE ||
        (type == EffectType::SPECIAL &&
        power > 0 &&
        (scope == TargetScope::SINGLE_ENEMY ||
          scope == TargetScope::ALL_ENEMIES ||
          scope == TargetScope::RANDOM_ENEMY));

    if (!isOffensive) {
        category = Category::OTHER;
    }
    else if (dependence == StatDependence::SEN) {
        category = Category::MELODY;
    }
    else {
        category = Category::PHYSICAL;
    }
  }
};

// main.ino

Item createItemById(int id) {
  
  // --- 0. 素材・換金アイテム (0-99) ---
  
  // 基本素材
  if (id == 1) return Item(1, "鉄くず", Item::ITEM_MATERIAL, 0, 10);
  if (id == 2) return Item(2, "銅の歯車", Item::ITEM_MATERIAL, 0, 30); // 名前修正(銅の歯車)
  
  // 進化アイテム (値段は適当に設定、売れるようにする)
  if (id == 10) return Item(10, "攻撃の歯車", Item::ITEM_MATERIAL, 0, 100);
  if (id == 11) return Item(11, "赤の歯車",   Item::ITEM_MATERIAL, 0, 100);
  if (id == 12) return Item(12, "紅の歯車",   Item::ITEM_MATERIAL, 0, 500);
  if (id == 13) return Item(13, "防御の歯車", Item::ITEM_MATERIAL, 0, 100);
  if (id == 14) return Item(14, "青の歯車",   Item::ITEM_MATERIAL, 0, 100);
  if (id == 15) return Item(15, "蒼の歯車",   Item::ITEM_MATERIAL, 0, 500);
  if (id == 16) return Item(16, "速度の歯車", Item::ITEM_MATERIAL, 0, 100);
  if (id == 17) return Item(17, "回復の歯車", Item::ITEM_MATERIAL, 0, 100);
  if (id == 18) return Item(18, "感応の歯車", Item::ITEM_MATERIAL, 0, 100);

  // (追加: 金の歯車など)
  if (id == 1010) return Item(1010, "銀の歯車", Item::ITEM_MATERIAL, 0, 200); // ID重複避けるなら変える
  // ※ 元コードにあった id=10,11 は上の進化アイテムと被っているので、
  // 銀の歯車などを別のIDにするか、あるいは上記のID構成に合わせる必要があります。
  // 今回は「進化アイテム」を優先し、銀・金は以下のようにします
  if (id == 3) return Item(3, "銀の歯車", Item::ITEM_MATERIAL, 0, 100);
  if (id == 4) return Item(4, "金の歯車", Item::ITEM_MATERIAL, 0, 500);
  if (id == 5) return Item(5, "謎のパーツ", Item::ITEM_MATERIAL, 0, 1000);


  // --- 1. 消費アイテム (100-199) ---
  if (id == 100) return Item(100, "リペアキット", Item::ITEM_CONSUMABLE, 50, 50);      // 50G
  if (id == 101) return Item(101, "リペアキット中", Item::ITEM_CONSUMABLE, 200, 150);  // 150G
  if (id == 102) return Item(102, "リペアキット大", Item::ITEM_CONSUMABLE, 9999, 500); // 500G
  if (id == 103) return Item(103, "エネルギー缶", Item::ITEM_CONSUMABLE, 20, 200);    // TP回復
  if (id == 104) return Item(104, "万能オイル", Item::ITEM_CONSUMABLE, 0, 100);       // 状態異常回復

  // --- 2. 巻物 (200-299) ---
  if (id >= 200 && id < 300) {
    int skillId = id - 200;
    static Skill tempSkill(skillId); 
    tempSkill = Skill(skillId);
    return Item(id, tempSkill.name, Item::ITEM_CONSUMABLE, 0, 500); 
  }

  // --- 3. 武器 (300-399) ---
  if (id == 300) return Item(300, "練習のタクト", Item::ITEM_WEAPON, 5, 50);
  if (id == 301) return Item(301, "鉄のタクト", Item::ITEM_WEAPON, 15, 300);
  if (id == 302) return Item(302, "強化タクト", Item::ITEM_WEAPON, 30, 1000);
  if (id == 303) return Item(303, "白銀のタクト", Item::ITEM_WEAPON, 50, 3500);
  if (id == 304) return Item(304, "近衛兵のバトン", Item::ITEM_WEAPON, 80, 9000);
  
  // ★ 宝箱限定 (最強)
  if (id == 399) return Item(399, "創世のタクト", Item::ITEM_WEAPON, 1500, 20000);

  // --- 4. 防具 (400-499) ---
  if (id == 400) return Item(400, "旅人のコート", Item::ITEM_ARMOR, 3, 30);
  if (id == 401) return Item(401, "レザーコート", Item::ITEM_ARMOR, 10, 250);
  if (id == 402) return Item(402, "強化スーツ", Item::ITEM_ARMOR, 20, 800);
  if (id == 403) return Item(403, "バトルスーツ", Item::ITEM_ARMOR, 35, 3000);
  if (id == 404) return Item(404, "指揮官の軍服", Item::ITEM_ARMOR, 60, 8000);

  // ★ 宝箱限定 (最強)
  if (id == 499) return Item(499, "イージス・ギア", Item::ITEM_ARMOR, 1200, 20000);

  // --- 5. アクセサリー (500-599) ---
  if (id == 500) return Item(500, "パワーリング", Item::ITEM_ACCESSORY, 10, 400); // ATK
  if (id == 501) return Item(501, "ガードリング", Item::ITEM_ACCESSORY, 10, 400); // DEF
  if (id == 502) return Item(502, "クイックブーツ", Item::ITEM_ACCESSORY, 10, 400); // SPD
  if (id == 503) return Item(503, "スナイパーレンズ", Item::ITEM_ACCESSORY, 10, 400); // SEN
  if (id == 504) return Item(504, "ラッキーコイン", Item::ITEM_ACCESSORY, 50, 400); // LCK
  
  // ★ 宝箱限定 (最強)
  if (id == 599) return Item(599, "トリニティ・コア", Item::ITEM_ACCESSORY, 500, 15000);

  // デフォルト
  return Item(id, "不明な品", Item::ITEM_MATERIAL, 0, 1);
}
// main.ino の Item クラスの後に追加

class Inventory {
public:
  // 所持品リスト
  struct ItemStack {
    Item item;
    int quantity;
  };
  std::vector<ItemStack> items;
  int money = 0;
  Inventory() {
    // 起動時に std::vector のメモリを
    // ある程度確保しておくと、後々の追加処理が高速になります
    items.reserve(20); // とりあえず20個分
  }

  // ★アイテムを追加する関数
  void addItem(const Item& newItem) {
    // 既に持っているか探す
    for (auto& stack : items) {
      if (stack.item.id == newItem.id) {
        stack.quantity++; // あったら個数を増やす
        return;
      }
    }
    // なかったら新しく追加 (個数1)
    items.push_back({newItem, 1});
  }

  int countItem(int id) {
    for (const auto& stack : items) {
      if (stack.item.id == id) {
        return stack.quantity;
      }
    }
    return 0;
  }

  bool removeItem(int id) {
    for (auto it = items.begin(); it != items.end(); ++it) {
      if (it->item.id == id) {
        it->quantity--;
        if (it->quantity <= 0) {
          items.erase(it); // 0個になったらリストから消す
        }
        return true;
      }
    }
    return false; // 見つからなかった
  }
  void removeByIndex(int index) {
      if (index < 0 || index >= items.size()) return;
      
      items[index].quantity--;
      if (items[index].quantity <= 0) {
          items.erase(items.begin() + index);
      }
  }
  // (将来的に、アイテム一覧を表示する関数なども追加)
  void saveTo(FsFile& file) {
    file.println(money);
    file.println(items.size());
    for (const auto& stack : items) {
      file.println(stack.item.id);
      file.println(stack.quantity);
    }
  }

  void loadFrom(FsFile& file) {
    money = file.readStringUntil('\n').toInt();
    int count = file.readStringUntil('\n').toInt();
    
    items.clear();
    for (int i = 0; i < count; i++) {
      int id = file.readStringUntil('\n').toInt();
      int qty = file.readStringUntil('\n').toInt();
      // アイテム生成してリストに追加
      Item item = createItemById(id);
      items.push_back({item, qty});
    }
  }
};

const int learnableSkillIDs[] = {
  // --- 攻撃系 ---
  1,  // ノイズ・ブラスト (TP:12)
  2,  // レゾナンス・ウェイブ (TP:25, 全体)
  3,  // ディソナンス (TP:20)
  
  // --- 回復・治療系 ---
  4,  // ファースト・エイド (TP:8)
  5,  // ピュリファイ (TP:10, 治療)
  6,  // ヒーリング・サークル (TP:30, 全体回復)

  // --- 補助・妨害系 ---
  7,  // チューニング・アタック (TP:15, ATK↑)
  8,  // チューニング・ガード (TP:15, DEF↑)
  9,  // アレグロ (TP:15, 全体SPD↑)
  10, // ラレンタンド (TP:12, 敵SPD↓)
  11, // ノイズ・ジャミング (TP:18, 全体ATK↓)

  // --- 奥義 (コスト高め) ---
  12, // グランド・シンフォニー (TP:60, 全体特大)
  13  // 完全調律 (TP:80, 全体全快)
};
const int learnableSkillCount = sizeof(learnableSkillIDs) / sizeof(int);

class Status{
private:
  int HP;
  int originalMaxHP;
  int MaxHP;
  //tune point
  int TP;
  int MaxTP;
  //物理攻撃に関係
  int Attack;
  //防御に関係
  int Defense;
  //回避率、命中率に関係
  int Speed;
  //旋律、ノイズ攻撃に使用
  int Sense;
  // ドロ率、クリ率に関係
  int Luck;
  int Level;
  int who;
  const char* name;
  int currentXP;
  int nextLevelXP;
  std::vector<Skill> learnedSkills; // 習得済みの旋律リスト
  int getPreEvolution(int currentId) {
    for (int i = 0; i < evolutionRuleCount; i++) {
      // 進化テーブルの「進化後(after)」が自分と一致したら、「進化前(before)」を返す
      if (evolutionTable[i].after_who_id == currentId) {
        return evolutionTable[i].before_who_id;
      }
    }
    return -1; // 進化前なし
  }
public:
  int equipWeaponId = -1; // 武器
  int equipArmorId = -1;  // 防具
  int equipAccId = -1;    // アクセ
  // --- 状態異常 ---
  int poisonTurns = 0;
  int poisonLevel = 0;   // 0: なし, 1: 毒, 2: 猛毒
  int paralyzedTurns = 0;
  int silencedTurns = 0;
  int confusedTurns = 0;
  // (他にも必要に応じて追加)
  int coverTurns = 0;
  // --- バフ/デバフ管理 ---
  // (効果量を float で、持続ターンを int で持つ)
    
  // バフ (Rateは倍率, 1.5 = 1.5倍)
  float atkBuffRate = 0;
  int atkBuffTurns = 0;
  float defBuffRate = 0;
  int defBuffTurns = 0;
  float spdBuffRate = 0;
  int spdBuffTurns = 0;
  float senBuffRate = 0;
  int senBuffTurns = 0;
  float lckBuffRate = 0;
  int lckBuffTurns = 0;
  float evaBuffRate = 0; // 回避率
  int evaBuffTurns = 0;

  // デバフ (Rateは倍率, 0.7 = 0.7倍)
  float atkDebuffRate = 0;
  int atkDebuffTurns = 0;
  float defDebuffRate = 0;
  int defDebuffTurns = 0;
  float spdDebuffRate = 0;
  int spdDebuffTurns = 0;
  float senDebuffRate = 0;
  int senDebuffTurns = 0;
  float lckDebuffRate = 0;
  int lckDebuffTurns = 0;

  // (HP/TPリジェネなどの特殊効果)
  int hpRegenTurns = 0;
  int tpRegenTurns = 0;
  // (その他、無敵、反射など)
  int invalidDamageTurns = 0; 
  int reflectPhysicalTurns = 0;
  int reflectMagicTurns = 0;
  int tauntTurns = 0;
  int twoActionsTurns = 0;
  int untargetableTurns = 0;
  int maxHpBuffTurns = 0;
  int physDamageOneTurns = 0;
  int endureTurns = 0;
  int counterTurns = 0;
  int autoReviveTurns = 0;
  int statusImmuneTurns = 0;
  int attributeResistTurns = 0;
  int cantMoveTurns = 0;
  int reflectAllTurns = 0;
  int damageGuardCount = 0;
  bool isDoubleAction = 0; // 2回行動
  bool isDefending = false;
  struct PopupData {
    int value;      // 数値
    bool isCritical; // 会心かどうか
  };
  std::vector<PopupData> popupValues; // int から PopupData に変更
  int getHp(){return HP;}
  void setHp(int val){ HP = val;}
  int getMaxHp(){return MaxHP;}
  int getTp(){return TP;}
  int getMaxTp(){return MaxTP;}
  int getAttack() {
    float finalValue = (float)this->Attack; // 基礎ATK
    // 武器の補正
    if (equipWeaponId != -1) {
      Item weapon = createItemById(equipWeaponId);
      finalValue += weapon.value; // 武器の攻撃力を足す
    }
    // アクセの補正 (例: パワーリング ID 500)
    if (equipAccId == 500) finalValue += 10;
    if (equipAccId == 599) finalValue += 500;
    // バフを適用 (例: 1.5倍 or 2.0倍)
    if (atkBuffTurns > 0) {
      finalValue *= atkBuffRate;
    }
    // デバフを適用 (例: 0.7倍 or 0.5倍)
    if (atkDebuffTurns > 0) {
      finalValue *= atkDebuffRate;
    }
    
    if (finalValue < 1) finalValue = 1;
    return (int)finalValue;
  }
  int getDefense() {
    float finalValue = (float)this->Defense; // 基礎DEF
    // 防具の補正
    if (equipArmorId != -1) {
      Item armor = createItemById(equipArmorId);
      finalValue += armor.value;
    }
    if (equipAccId == 501) finalValue += 10;  // ガードリング
    if (equipAccId == 599) finalValue += 500; // トリニティ・コア
    if (defBuffTurns > 0) {
        finalValue *= defBuffRate;
    }
    if (defDebuffTurns > 0) {
        finalValue *= defDebuffRate;
    }

    if (finalValue < 1) finalValue = 1;
    return (int)finalValue;
  }
  int getSpeed() {
    float finalValue = (float)this->Speed; // 基礎SPD
    // アクセ補正
    if (equipAccId == 502) finalValue += 10;  // クイックブーツ
    if (equipAccId == 599) finalValue += 500; // トリニティ・コア
    if (spdBuffTurns > 0) {
        finalValue *= spdBuffRate;
    }
    if (spdDebuffTurns > 0) {
        finalValue *= spdDebuffRate;
    }

    if (finalValue < 1) finalValue = 1;
    return (int)finalValue;
  }
  int getSense() {
    float finalValue = (float)this->Sense; // 基礎SEN
    // アクセ補正
    if (equipAccId == 503) finalValue += 10;  // スナイパーレンズ
    if (equipAccId == 599) finalValue += 500; // トリニティ・コア
    if (senBuffTurns > 0) {
        finalValue *= senBuffRate;
    }
    if (senDebuffTurns > 0) {
        finalValue *= senDebuffRate;
    }

    if (finalValue < 1) finalValue = 1;
    return (int)finalValue;
  }
  int getLuck() {
    float finalValue = (float)this->Luck; // 基礎LCK
    // アクセ補正
    if (equipAccId == 504) finalValue += 50;  // ラッキーコイン
    if (equipAccId == 599) finalValue += 500; // トリニティ・コア

    if (lckBuffTurns > 0) {
        finalValue *= lckBuffRate;
    }
    if (lckDebuffTurns > 0) {
        finalValue *= lckDebuffRate;
    }

    if (finalValue < 1) finalValue = 1;
    return (int)finalValue;
  }
  int getLevel(){return Level;}
  int getXP(){ return currentXP; }
  int getNextXP(){ return nextLevelXP; }
  int getWho(){ return who; }
  const char* getname(){return name;}
  int getPoisonTurns() const { return poisonTurns; }
  int getParalyzedTurns() const { return paralyzedTurns; }
  int getSilencedTurns() const { return silencedTurns; }
  int getConfusedTurns() const { return confusedTurns; }
  int normalizeWho(int w) {
    if (w >= 0 && w <= 37) return w + 39;
    return w; 
  }
  void updateName() {
    int wd = normalizeWho(who);
    switch (wd) {
      case 38: name = "調律師"; break;
      case 39: name = "ストライカー"; break;
      case 40: name = "ガーディアン"; break;
      case 41: name = "クリッパー"; break;
      case 42: name = "メンダー"; break;
      case 43: name = "ジャマー"; break;
      // 1段階目
      case 44: name = "ギア・ソルジャー"; break;
      case 45: name = "フォートレス"; break;
      case 46: name = "ブレード・ダンサー"; break;
      case 47: name = "ハーモニスト"; break;
      case 48: name = "ディスアレンジャー"; break;
      // 2段階目
      case 49: name = "ギア・ナイト"; break;
      case 50: name = "キャッスル・ウォール"; break;
      case 51: name = "サイクロン・ダンサー"; break;
      case 52: name = "コンダクター"; break;
      case 53: name = "カオス・ジャマー"; break;
      // 3段階目
      case 54: name = "ヴァンガード"; break;
      case 55: name = "スワッシュバックラー"; break;
      case 56: name = "バスティオン"; break;
      case 57: name = "イージス"; break;
      case 58: name = "テンペスト"; break;
      case 59: name = "マエストロ"; break;
      case 60: name = "ディスコード"; break;
      // 4段階目
      case 61: name = "オーバーロード"; break;
      case 62: name = "デストロイヤー"; break;
      case 63: name = "ゼロ・ブレード"; break;
      case 64: name = "ヴォイド・ストーカー"; break;
      case 65: name = "アダマンタイト"; break;
      case 66: name = "インヴィンシブル"; break;
      case 67: name = "ディヴァイン・シールド"; break;
      case 68: name = "リジェネレーター"; break;
      case 69: name = "シルフィード"; break;
      case 70: name = "アクセラレーター"; break;
      case 71: name = "アーク・ハーモニスト"; break;
      case 72: name = "シンフォニア"; break;
      case 73: name = "パンデモニウム"; break;
      case 74: name = "ジョーカー"; break;
      // 特殊
      case 75: name = "はぐれノイズ"; break;
      case 76: name = "ノイズ・キング"; break;
      case 80: name = "スプラウト・ギア"; break;
      case 81: name = "ソレイユ"; break;
      case 82: name = "ハーベスト・スティンガー"; break;
      case 83: name = "雪影"; break;
      case 84: name = "デウス・エクス・マキナ"; break;

      default: name = "???"; break;
    }
  }
  enum EvolutionTriggerType {
    TRIGGER_LEVEL, // レベルアップ
    TRIGGER_ITEM   // アイテム使用
  };
  float getEvasionBonus() {
    float bonus = 1.0; // 通常 1.0倍

    if (evaBuffTurns > 0) {
        bonus *= evaBuffRate;
    }
    
    return bonus;
  }
  struct SkillLearningRule {
    int who_id; // 対象のID (例: 39)
    int level;  // 習得レベル (例: 10)
    int skill_id; // 習得する旋律のID (例: 101)
  };
  static const SkillLearningRule skillLearningTable[];
  static const int skillLearningRuleCount;

  struct EvolutionRule {
    int before_who_id;
    EvolutionTriggerType trigger_type;
    int trigger_value; 
    int after_who_id;
  };

  static const EvolutionRule evolutionTable[];
  static const int evolutionRuleCount;
  std::vector<Skill>& getLearnedSkills() {
    return learnedSkills;
  }

  int decide_MaxHP(int l, int who){
    if(who == 0) return l * 3 + 12; // 0:ストライカー (並)
    if(who == 1) return l * 5 + 15; // 1:ガーディアン (高い)
    if(who == 2) return l * 2 + 8;  // 2:クリッパー (低い)
    if(who == 3) return l * 3 + 12; // 3:メンダー (並)
    if(who == 4) return l * 2 + 10; // 4:ジャマー (低い)

    // 1段階目進化
    if(who == 5) return l * 4 + 15; // 5:ギア・ソルジャー (並+)
    if(who == 6) return l * 6 + 20; // 6:フォートレス (高い+)
    if(who == 7) return l * 3 + 10; // 7:ブレード・ダンサー (低い+)
    if(who == 8) return l * 4 + 14; // 8:ハーモニスト (並+)
    if(who == 9) return l * 3 + 12; // 9:ディスアレンジャー (低い+)
    // 2段階目進化 (10-14)
    if(who == 10) return l * 5 + 20; // 10:ギア・ナイト (並++)
    if(who == 11) return l * 7 + 25; // 11:キャッスル・ウォール (高い++)
    if(who == 12) return l * 4 + 12; // 12:サイクロン・ダンサー (低い++)
    if(who == 13) return l * 5 + 16; // 13:コンダクター (並++)
    if(who == 14) return l * 4 + 14; // 14:カオス・ジャマー (低い++)
    // 3段階目進化 (15-21)
    if(who == 15) return l * 6 + 25; // 15:ヴァンガード (純ATK)
    if(who == 16) return l * 5 + 20; // 16:スワッシュバックラー (ATK+SPD)
    if(who == 17) return l * 8 + 30; // 17:バスティオン (純DEF)
    if(who == 18) return l * 10 + 40; // 18:イージス (DEF+HP)
    if(who == 19) return l * 5 + 15; // 19:テンペスト (SPD)
    if(who == 20) return l * 6 + 18; // 20:マエストロ (SEN)
    if(who == 21) return l * 5 + 16; // 21:ディスコード (LCK)
    // 4段階目 (22-35)
    if(who == 22) return l * 8 + 30;  // 22:オーバーロード (バランス)
    if(who == 23) return l * 6 + 25;  // 23:デストロイヤー (ATK特化)
    if(who == 24) return l * 6 + 22;  // 24:ゼロ・ブレード (ATK/SPD)
    if(who == 25) return l * 5 + 20;  // 25:ヴォイド・ストーカー (SPD/LCK)
    if(who == 26) return l * 9 + 35;  // 26:アダマンタイト (純DEF)
    if(who == 27) return l * 12 + 50; // 27:インヴィンシブル (DEF+HP)
    if(who == 28) return l * 10 + 40; // 28:ディヴァイン・シールド (DEF/SEN)
    if(who == 29) return l * 12 + 50; // 29:リジェネレーター (HP/SEN)
    if(who == 30) return l * 6 + 18;  // 30:シルフィード (SPD/LCK)
    if(who == 31) return l * 6 + 20;  // 31:アクセラレーター (SPD/ATK)
    if(who == 32) return l * 7 + 20;  // 32:アーク・ハーモニスト (純SEN)
    if(who == 33) return l * 8 + 22;  // 33:シンフォニア (万能SEN)
    if(who == 34) return l * 7 + 18;  // 34:パンデモニウム (LCK/SEN)
    if(who == 35) return l * 6 + 18;  // 35:ジョーカー (LCK/SPD)
    // 特殊 (36-37)
    if(who == 36) return 8;  // 36:はぐれノイズ (HP固定)
    if(who == 37) return 12; // 37:ノイズ・キング (HP固定)

    //主人公
    if(who == 38) return l * 3 + 20;

    //仲間
    if(who == 39) return l * 3 + 12;
    if(who == 40) return l * 5 + 15;
    if(who == 41) return l * 2 + 8;
    if(who == 42) return l * 3 + 12;
    if(who == 43) return l * 2 + 10;
    //1段階進化
    if(who == 44) return l * 4 + 15;
    if(who == 45) return l * 6 + 20;
    if(who == 46) return l * 3 + 10;
    if(who == 47) return l * 4 + 14;
    if(who == 48) return l * 3 + 12;
    // 2段階目進化 (10-14)
    if(who == 49) return l * 5 + 20; // 10:ギア・ナイト (並++)
    if(who == 50) return l * 7 + 25; // 11:キャッスル・ウォール (高い++)
    if(who == 51) return l * 4 + 12; // 12:サイクロン・ダンサー (低い++)
    if(who == 52) return l * 5 + 16; // 13:コンダクター (並++)
    if(who == 53) return l * 4 + 14; // 14:カオス・ジャマー (低い++)
    // 3段階目進化 (15-21)
    if(who == 54) return l * 6 + 25; // 15:ヴァンガード (純ATK)
    if(who == 55) return l * 5 + 20; // 16:スワッシュバックラー (ATK+SPD)
    if(who == 56) return l * 8 + 30; // 17:バスティオン (純DEF)
    if(who == 57) return l * 10 + 40; // 18:イージス (DEF+HP)
    if(who == 58) return l * 5 + 15; // 19:テンペスト (SPD)
    if(who == 59) return l * 6 + 18; // 20:マエストロ (SEN)
    if(who == 60) return l * 5 + 16; // 21:ディスコード (LCK)
    // 4段階目 (22-35)
    if(who == 61) return l * 8 + 30;  // 22:オーバーロード (バランス)
    if(who == 62) return l * 6 + 25;  // 23:デストロイヤー (ATK特化)
    if(who == 63) return l * 6 + 22;  // 24:ゼロ・ブレード (ATK/SPD)
    if(who == 64) return l * 5 + 20;  // 25:ヴォイド・ストーカー (SPD/LCK)
    if(who == 65) return l * 9 + 35;  // 26:アダマンタイト (純DEF)
    if(who == 66) return l * 12 + 50; // 27:インヴィンシブル (DEF+HP)
    if(who == 67) return l * 10 + 40; // 28:ディヴァイン・シールド (DEF/SEN)
    if(who == 68) return l * 12 + 50; // 29:リジェネレーター (HP/SEN)
    if(who == 69) return l * 6 + 18;  // 30:シルフィード (SPD/LCK)
    if(who == 70) return l * 6 + 20;  // 31:アクセラレーター (SPD/ATK)
    if(who == 71) return l * 7 + 20;  // 32:アーク・ハーモニスト (純SEN)
    if(who == 72) return l * 8 + 22;  // 33:シンフォニア (万能SEN)
    if(who == 73) return l * 7 + 18;  // 34:パンデモニウム (LCK/SEN)
    if(who == 74) return l * 6 + 18;  // 35:ジョーカー (LCK/SPD)
    if(who == 80) return 500;
    if(who == 81) return 1200;
    if(who == 82) return 3000;
    if(who == 83) return 8000;
    if(who == 84) return 20000;
    // 特殊 (36-37)
    if(who == 36) return l + 8;  // 36:はぐれノイズ (HP固定)
    if(who == 37) return l * 2 + 12; // 37:ノイズ・キング (HP固定)
    return 0;
  }
  int decide_MaxTP(int l, int who){
    if(who == 0) return l * 1 + 5;  // 0:ストライカー (低い)
    if(who == 1) return l * 1 + 5;  // 1:ガーディアン (低い)
    if(who == 2) return l * 2 + 10; // 2:クリッパー (並)
    if(who == 3) return l * 5 + 15; // 3:メンダー (高い)
    if(who == 4) return l * 4 + 10; // 4:ジャマー (高い)
    // 1段階目進化
    if(who == 5) return l * 1 + 6;  // 5:ギア・ソルジャー (低い)
    if(who == 6) return l * 1 + 6;  // 6:フォートレス (低い)
    if(who == 7) return l * 2 + 12; // 7:ブレード・ダンサー (並)
    if(who == 8) return l * 6 + 18; // 8:ハーモニスト (高い+)
    if(who == 9) return l * 5 + 12; // 9:ディスアレンジャー (高い+)
    // 2段階目進化 (10-14)
    if(who == 10) return l * 1 + 7;  // 10:ギア・ナイト (低い)
    if(who == 11) return l * 1 + 7;  // 11:キャッスル・ウォール (低い)
    if(who == 12) return l * 2 + 15; // 12:サイクロン・ダンサー (並)
    if(who == 13) return l * 7 + 22; // 13:コンダクター (高い++)
    if(who == 14) return l * 6 + 15; // 14:カオス・ジャマー (高い++)
    // 3段階目 (15-21)
    if(who == 15) return l * 1 + 8;  // 15:ヴァンガード
    if(who == 16) return l * 2 + 10; // 16:スワッシュバックラー
    if(who == 17) return l * 1 + 8;  // 17:バスティオン
    if(who == 18) return l * 4 + 20; // 18:イージス
    if(who == 19) return l * 3 + 18; // 19:テンペスト
    if(who == 20) return l * 9 + 30; // 20:マエストロ
    if(who == 21) return l * 8 + 25; // 21:ディスコード
    // 4段階目 (22-35)
    if(who == 22) return l * 2 + 10;  // 22:オーバーロード
    if(who == 23) return l * 1 + 8;   // 23:デストロイヤー
    if(who == 24) return l * 3 + 12;  // 24:ゼロ・ブレード
    if(who == 25) return l * 3 + 15;  // 25:ヴォイド・ストーカー
    if(who == 26) return l * 1 + 10;  // 26:アダマンタイト
    if(who == 27) return l * 2 + 10;  // 27:インヴィンシブル
    if(who == 28) return l * 6 + 25;  // 28:ディヴァイン・シールド
    if(who == 29) return l * 7 + 30;  // 29:リジェネレーター
    if(who == 30) return l * 4 + 20;  // 30:シルフィード
    if(who == 31) return l * 3 + 18;  // 31:アクセラレーター
    if(who == 32) return l * 12 + 40; // 32:アーク・ハーモニスト
    if(who == 33) return l * 10 + 35; // 33:シンフォニア
    if(who == 34) return l * 11 + 30; // 34:パンデモニウム
    if(who == 35) return l * 10 + 28; // 35:ジョーカー
    // 特殊 (36-37)
    if(who == 36) return 0; // 36:はぐれノイズ (TPなし)
    if(who == 37) return 0; // 37:ノイズ・キング (TPなし)

    //主人公
    if(who == 38) return l * 3 + 20;
    //仲間
    if(who == 39) return l * 1 + 5;
    if(who == 40) return l * 1 + 5;  // 1:ガーディアン (低い)
    if(who == 41) return l * 2 + 10; // 2:クリッパー (並)
    if(who == 42) return l * 5 + 15; // 3:メンダー (高い)
    if(who == 43) return l * 4 + 10; // 4:ジャマー (高い)
    // 1段階目進化
    if(who == 44) return l * 1 + 6;  // 5:ギア・ソルジャー (低い)
    if(who == 45) return l * 1 + 6;  // 6:フォートレス (低い)
    if(who == 46) return l * 2 + 12; // 7:ブレード・ダンサー (並)
    if(who == 47) return l * 6 + 18; // 8:ハーモニスト (高い+)
    if(who == 48) return l * 5 + 12; // 9:ディスアレンジャー (高い+)
    // 2段階目進化 (10-14)
    if(who == 49) return l * 1 + 7;  // 10:ギア・ナイト (低い)
    if(who == 50) return l * 1 + 7;  // 11:キャッスル・ウォール (低い)
    if(who == 51) return l * 2 + 15; // 12:サイクロン・ダンサー (並)
    if(who == 52) return l * 7 + 22; // 13:コンダクター (高い++)
    if(who == 53) return l * 6 + 15; // 14:カオス・ジャマー (高い++)
    // 3段階目 (15-21)
    if(who == 54) return l * 1 + 8;  // 15:ヴァンガード
    if(who == 55) return l * 2 + 10; // 16:スワッシュバックラー
    if(who == 56) return l * 1 + 8;  // 17:バスティオン
    if(who == 57) return l * 4 + 20; // 18:イージス
    if(who == 58) return l * 3 + 18; // 19:テンペスト
    if(who == 59) return l * 9 + 30; // 20:マエストロ
    if(who == 60) return l * 8 + 25; // 21:ディスコード
    // 4段階目 (22-35)
    if(who == 61) return l * 2 + 10;  // 22:オーバーロード
    if(who == 62) return l * 1 + 8;   // 23:デストロイヤー
    if(who == 63) return l * 3 + 12;  // 24:ゼロ・ブレード
    if(who == 64) return l * 3 + 15;  // 25:ヴォイド・ストーカー
    if(who == 65) return l * 1 + 10;  // 26:アダマンタイト
    if(who == 66) return l * 2 + 10;  // 27:インヴィンシブル
    if(who == 67) return l * 6 + 25;  // 28:ディヴァイン・シールド
    if(who == 68) return l * 7 + 30;  // 29:リジェネレーター
    if(who == 69) return l * 4 + 20;  // 30:シルフィード
    if(who == 70) return l * 3 + 18;  // 31:アクセラレーター
    if(who == 71) return l * 12 + 40; // 32:アーク・ハーモニスト
    if(who == 72) return l * 10 + 35; // 33:シンフォニア
    if(who == 73) return l * 11 + 30; // 34:パンデモニウム
    if(who == 74) return l * 10 + 28; // 35:ジョーカー
    // 特殊 (36-37)
    if(who == 75) return 0; // 36:はぐれノイズ (TPなし)
    if(who == 76) return 0; // 37:ノイズ・キング (TPなし)
    return 0;
  }
  int decide_Attack(int l, int who){
    if(who == 0) return l * 5 + 5;  // 0:ストライカー (高い)
    if(who == 1) return l * 2 + 3;  // 1:ガーディアン (低い)
    if(who == 2) return l * 3 + 3;  // 2:クリッパー (並)
    if(who == 3) return l * 1 + 2;  // 3:メンダー (最低)
    if(who == 4) return l * 1 + 2;  // 4:ジャマー (最低)
    // 1段階目進化
    if(who == 5) return l * 6 + 8;  // 5:ギア・ソルジャー (高い+)
    if(who == 6) return l * 2 + 4;  // 6:フォートレス (低い)
    if(who == 7) return l * 4 + 4;  // 7:ブレード・ダンサー (並+)
    if(who == 8) return l * 1 + 2;  // 8:ハーモニスト (最低)
    if(who == 9) return l * 1 + 2;  // 9:ディスアレンジャー (最低)
    // 2段階目進化 (10-14)
    if(who == 10) return l * 7 + 12; // 10:ギア・ナイト (高い++)
    if(who == 11) return l * 2 + 5;  // 11:キャッスル・ウォール (低い)
    if(who == 12) return l * 5 + 6;  // 12:サイクロン・ダンサー (並++)
    if(who == 13) return l * 1 + 2;  // 13:コンダクター (最低)
    if(who == 14) return l * 1 + 2;  // 14:カオス・ジャマー (最低)
    // 3段階目 (15-21)
    if(who == 15) return l * 9 + 15; // 15:ヴァンガード (純ATK)
    if(who == 16) return l * 8 + 13; // 16:スワッシュバックラー (ATK+SPD)
    if(who == 17) return l * 2 + 6;  // 17:バスティオン
    if(who == 18) return l * 2 + 6;  // 18:イージス
    if(who == 19) return l * 6 + 8;  // 19:テンペスト
    if(who == 20) return l * 1 + 2;  // 20:マエストロ
    if(who == 21) return l * 1 + 2;  // 21:ディスコード
    // 4段階目 (22-35)
    if(who == 22) return l * 10 + 20; // 22:オーバーロード
    if(who == 23) return l * 12 + 25; // 23:デストロイヤー
    if(who == 24) return l * 10 + 15; // 24:ゼロ・ブレード
    if(who == 25) return l * 8 + 10;  // 25:ヴォイド・ストーカー
    if(who == 26) return l * 3 + 8;   // 26:アダマンタイト
    if(who == 27) return l * 3 + 8;   // 27:インヴィンシブル
    if(who == 28) return l * 4 + 8;   // 28:ディヴァイン・シールド
    if(who == 29) return l * 3 + 7;   // 29:リジェネレーター
    if(who == 30) return l * 7 + 10;  // 30:シルフィード
    if(who == 31) return l * 9 + 12;  // 31:アクセラレーター
    if(who == 32) return l * 1 + 2;   // 32:アーク・ハーモニスト
    if(who == 33) return l * 5 + 5;   // 33:シンフォニア
    if(who == 34) return l * 2 + 3;   // 34:パンデモニウム
    if(who == 35) return l * 6 + 6;   // 35:ジョーカー
    // 特殊 (36-37)
    if(who == 36) return l * 1 + 1; // 36:はぐれノイズ (攻撃しない)
    if(who == 37) return l * 1 + 1; // 37:ノイズ・キング (攻撃しない)

    //主人公
    if(who == 38) return l * 3 + 20;
    //仲間
    if(who == 39) return l * 5 + 5;
    if(who == 40) return l * 2 + 3;  // 1:ガーディアン (低い)
    if(who == 41) return l * 3 + 3;  // 2:クリッパー (並)
    if(who == 42) return l * 1 + 2;  // 3:メンダー (最低)
    if(who == 43) return l * 1 + 2;  // 4:ジャマー (最低)
    // 1段階目進化
    if(who == 44) return l * 6 + 8;  // 5:ギア・ソルジャー (高い+)
    if(who == 45) return l * 2 + 4;  // 6:フォートレス (低い)
    if(who == 46) return l * 4 + 4;  // 7:ブレード・ダンサー (並+)
    if(who == 47) return l * 1 + 2;  // 8:ハーモニスト (最低)
    if(who == 48) return l * 1 + 2;  // 9:ディスアレンジャー (最低)
    // 2段階目進化 (10-14)
    if(who == 49) return l * 7 + 12; // 10:ギア・ナイト (高い++)
    if(who == 50) return l * 2 + 5;  // 11:キャッスル・ウォール (低い)
    if(who == 51) return l * 5 + 6;  // 12:サイクロン・ダンサー (並++)
    if(who == 52) return l * 1 + 2;  // 13:コンダクター (最低)
    if(who == 53) return l * 1 + 2;  // 14:カオス・ジャマー (最低)
    // 3段階目 (15-21)
    if(who == 54) return l * 9 + 15; // 15:ヴァンガード (純ATK)
    if(who == 55) return l * 8 + 13; // 16:スワッシュバックラー (ATK+SPD)
    if(who == 56) return l * 2 + 6;  // 17:バスティオン
    if(who == 57) return l * 2 + 6;  // 18:イージス
    if(who == 58) return l * 6 + 8;  // 19:テンペスト
    if(who == 59) return l * 1 + 2;  // 20:マエストロ
    if(who == 60) return l * 1 + 2;  // 21:ディスコード
    // 4段階目 (22-35)
    if(who == 61) return l * 10 + 20; // 22:オーバーロード
    if(who == 62) return l * 12 + 25; // 23:デストロイヤー
    if(who == 63) return l * 10 + 15; // 24:ゼロ・ブレード
    if(who == 64) return l * 8 + 10;  // 25:ヴォイド・ストーカー
    if(who == 65) return l * 3 + 8;   // 26:アダマンタイト
    if(who == 66) return l * 3 + 8;   // 27:インヴィンシブル
    if(who == 67) return l * 4 + 8;   // 28:ディヴァイン・シールド
    if(who == 68) return l * 3 + 7;   // 29:リジェネレーター
    if(who == 69) return l * 7 + 10;  // 30:シルフィード
    if(who == 70) return l * 9 + 12;  // 31:アクセラレーター
    if(who == 71) return l * 1 + 2;   // 32:アーク・ハーモニスト
    if(who == 72) return l * 5 + 5;   // 33:シンフォニア
    if(who == 73) return l * 2 + 3;   // 34:パンデモニウム
    if(who == 74) return l * 6 + 6;   // 35:ジョーカー
    // 特殊 (36-37)
    if(who == 75) return l * 1 + 1; // 36:はぐれノイズ (攻撃しない)
    if(who == 76) return l * 1 + 1; // 37:ノイズ・キング (攻撃しない)
    
    return 0;
  }
  int decide_Defense(int l, int who){
    if(who == 0) return l * 1 + 3;  // 0:ストライカー (低い)
    if(who == 1) return l * 5 + 5;  // 1:ガーディアン (高い)
    if(who == 2) return l * 1 + 3;  // 2:クリッパー (低い)
    if(who == 3) return l * 3 + 5;  // 3:メンダー (並)
    if(who == 4) return l * 3 + 5;  // 4:ジャマー (並)
    // 1段階目進化
    if(who == 5) return l * 1 + 5;  // 5:ギア・ソルジャー (低い+)
    if(who == 6) return l * 6 + 8;  // 6:フォートレス (高い+)
    if(who == 7) return l * 1 + 4;  // 7:ブレード・ダンサー (低い+)
    if(who == 8) return l * 3 + 7;  // 8:ハーモニスト (並+)
    if(who == 9) return l * 3 + 6;  // 9:ディスアレンジャー (並)
    // 2段階目進化 (10-14)
    if(who == 10) return l * 1 + 6;  // 10:ギア・ナイト (低い+)
    if(who == 11) return l * 7 + 12; // 11:キャッスル・ウォール (高い++)
    if(who == 12) return l * 1 + 5;  // 12:サイクロン・ダンサー (低い+)
    if(who == 13) return l * 4 + 9;  // 13:コンダクター (並++)
    if(who == 14) return l * 4 + 8;  // 14:カオス・ジャマー (並+)
    // 3段階目 (15-21)
    if(who == 15) return l * 3 + 8;  // 15:ヴァンガード (重装甲)
    if(who == 16) return l * 1 + 6;  // 16:スワッシュバックラー (軽装)
    if(who == 17) return l * 9 + 18; // 17:バスティオン (純DEF)
    if(who == 18) return l * 8 + 15; // 18:イージス (DEF+HP)
    if(who == 19) return l * 1 + 6;  // 19:テンペスト
    if(who == 20) return l * 5 + 11; // 20:マエストロ
    if(who == 21) return l * 5 + 10; // 21:ディスコード
    // 4段階目 (22-35)
    if(who == 22) return l * 6 + 10;  // 22:オーバーロード
    if(who == 23) return l * 1 + 5;   // 23:デストロイヤー
    if(who == 24) return l * 2 + 7;   // 24:ゼロ・ブレード
    if(who == 25) return l * 1 + 6;   // 25:ヴォイド・ストーカー
    if(who == 26) return l * 12 + 25; // 26:アダマンタイト
    if(who == 27) return l * 10 + 20; // 27:インヴィンシブル
    if(who == 28) return l * 10 + 18; // 28:ディヴァイン・シールド
    if(who == 29) return l * 8 + 15;  // 29:リジェネレーター
    if(who == 30) return l * 3 + 8;   // 30:シルフィード
    if(who == 31) return l * 2 + 7;   // 31:アクセラレーター
    if(who == 32) return l * 6 + 12;  // 32:アーク・ハーモニスト
    if(who == 33) return l * 7 + 14;  // 33:シンフォニア
    if(who == 34) return l * 6 + 12;  // 34:パンデモニウム
    if(who == 35) return l * 5 + 10;  // 35:ジョーカー
    // 特殊 (36-37)
    if(who == 36) return l * 500 + 200; // 36:はぐれノイズ (超防御)
    if(who == 37) return l * 700 + 300; // 37:ノイズ・キング (極防御)

    //主人公
    if(who == 38) return l * 3 + 20;
    //仲間
    if(who == 39) return l * 1 + 3;  // 0:ストライカー (低い)
    if(who == 40) return l * 5 + 5;  // 1:ガーディアン (高い)
    if(who == 41) return l * 1 + 3;  // 2:クリッパー (低い)
    if(who == 42) return l * 3 + 5;  // 3:メンダー (並)
    if(who == 43) return l * 3 + 5;  // 4:ジャマー (並)
    // 1段階目進化
    if(who == 44) return l * 1 + 5;  // 5:ギア・ソルジャー (低い+)
    if(who == 45) return l * 6 + 8;  // 6:フォートレス (高い+)
    if(who == 46) return l * 1 + 4;  // 7:ブレード・ダンサー (低い+)
    if(who == 47) return l * 3 + 7;  // 8:ハーモニスト (並+)
    if(who == 48) return l * 3 + 6;  // 9:ディスアレンジャー (並)
    // 2段階目進化 (10-14)
    if(who == 49) return l * 1 + 6;  // 10:ギア・ナイト (低い+)
    if(who == 50) return l * 7 + 12; // 11:キャッスル・ウォール (高い++)
    if(who == 51) return l * 1 + 5;  // 12:サイクロン・ダンサー (低い+)
    if(who == 52) return l * 4 + 9;  // 13:コンダクター (並++)
    if(who == 53) return l * 4 + 8;  // 14:カオス・ジャマー (並+)
    // 3段階目 (15-21)
    if(who == 54) return l * 3 + 8;  // 15:ヴァンガード (重装甲)
    if(who == 55) return l * 1 + 6;  // 16:スワッシュバックラー (軽装)
    if(who == 56) return l * 9 + 18; // 17:バスティオン (純DEF)
    if(who == 57) return l * 8 + 15; // 18:イージス (DEF+HP)
    if(who == 58) return l * 1 + 6;  // 19:テンペスト
    if(who == 59) return l * 5 + 11; // 20:マエストロ
    if(who == 60) return l * 5 + 10; // 21:ディスコード
    // 4段階目 (22-35)
    if(who == 61) return l * 6 + 10;  // 22:オーバーロード
    if(who == 62) return l * 1 + 5;   // 23:デストロイヤー
    if(who == 63) return l * 2 + 7;   // 24:ゼロ・ブレード
    if(who == 64) return l * 1 + 6;   // 25:ヴォイド・ストーカー
    if(who == 65) return l * 12 + 25; // 26:アダマンタイト
    if(who == 66) return l * 10 + 20; // 27:インヴィンシブル
    if(who == 67) return l * 10 + 18; // 28:ディヴァイン・シールド
    if(who == 68) return l * 8 + 15;  // 29:リジェネレーター
    if(who == 69) return l * 3 + 8;   // 30:シルフィード
    if(who == 70) return l * 2 + 7;   // 31:アクセラレーター
    if(who == 71) return l * 6 + 12;  // 32:アーク・ハーモニスト
    if(who == 72) return l * 7 + 14;  // 33:シンフォニア
    if(who == 73) return l * 6 + 12;  // 34:パンデモニウム
    if(who == 74) return l * 5 + 10;  // 35:ジョーカー
    // 特殊 (36-37)
    if(who == 75) return l * 500 + 200; // 36:はぐれノイズ (超防御)
    if(who == 76) return l * 700 + 300; // 37:ノイズ・キング (極防御)

    return 0;
  }
  int decide_Speed(int l, int who){
    if(who == 0) return l * 3 + 3;  // 0:ストライカー (並)
    if(who == 1) return l * 1 + 2;  // 1:ガーディアン (最低)
    if(who == 2) return l * 5 + 5;  // 2:クリッパー (高い)
    if(who == 3) return l * 2 + 5;  // 3:メンダー (低い)
    if(who == 4) return l * 4 + 3;  // 4:ジャマー (高い)
    // 1段階目進化
    if(who == 5) return l * 3 + 5;  // 5:ギア・ソルジャー (並)
    if(who == 6) return l * 1 + 2;  // 6:フォートレス (最低)
    if(who == 7) return l * 6 + 8;  // 7:ブレード・ダンサー (高い+)
    if(who == 8) return l * 2 + 5;  // 8:ハーモニスト (低い)
    if(who == 9) return l * 5 + 4;  // 9:ディスアレンジャー (高い+)
    // 2段階目進化 (10-14)
    if(who == 10) return l * 3 + 6;  // 10:ギア・ナイト (並)
    if(who == 11) return l * 1 + 2;  // 11:キャッスル・ウォール (最低)
    if(who == 12) return l * 7 + 12; // 12:サイクロン・ダンサー (高い++)
    if(who == 13) return l * 2 + 6;  // 13:コンダクター (低い)
    if(who == 14) return l * 6 + 6;  // 14:カオス・ジャマー (高い++)
    // 3段階目 (15-21)
    if(who == 15) return l * 2 + 7;  // 15:ヴァンガード (遅い)
    if(who == 16) return l * 7 + 10; // 16:スワッシュバックラー (速い)
    if(who == 17) return l * 1 + 2;  // 17:バスティオン
    if(who == 18) return l * 2 + 3;  // 18:イージス
    if(who == 19) return l * 9 + 15; // 19:テンペスト (最速)
    if(who == 20) return l * 3 + 7;  // 20:マエストロ
    if(who == 21) return l * 7 + 8;  // 21:ディスコード
    // 4段階目 (22-35)
    if(who == 22) return l * 3 + 8;   // 22:オーバーロード
    if(who == 23) return l * 2 + 7;   // 23:デストロイヤー
    if(who == 24) return l * 9 + 12;  // 24:ゼロ・ブレード
    if(who == 25) return l * 10 + 15; // 25:ヴォイド・ストーカー
    if(who == 26) return l * 1 + 2;   // 26:アダマンタイト
    if(who == 27) return l * 1 + 2;   // 27:インヴィンシブル
    if(who == 28) return l * 3 + 5;   // 28:ディヴァイン・シールド
    if(who == 29) return l * 2 + 4;   // 29:リジェネレーター
    if(who == 30) return l * 11 + 18; // 30:シルフィード
    if(who == 31) return l * 10 + 16; // 31:アクセラレーター
    if(who == 32) return l * 4 + 8;   // 32:アーク・ハーモニスト
    if(who == 33) return l * 6 + 10;  // 33:シンフォニア
    if(who == 34) return l * 8 + 10;  // 34:パンデモニウム
    if(who == 35) return l * 9 + 12;  // 35:ジョーカー
    // 特殊 (36-37)
    if(who == 36) return l * 10 + 50; // 36:はぐれノイズ (超素早さ)
    if(who == 37) return l * 12 + 60; // 37:ノイズ・キング (極素早さ)

    //主人公
    if(who == 38) return l * 3 + 20;
    //仲間
    if(who == 39) return l * 3 + 3;  // 0:ストライカー (並)
    if(who == 40) return l * 1 + 2;  // 1:ガーディアン (最低)
    if(who == 41) return l * 5 + 5;  // 2:クリッパー (高い)
    if(who == 42) return l * 2 + 5;  // 3:メンダー (低い)
    if(who == 43) return l * 4 + 3;  // 4:ジャマー (高い)
    // 1段階目進化
    if(who == 44) return l * 3 + 5;  // 5:ギア・ソルジャー (並)
    if(who == 45) return l * 1 + 2;  // 6:フォートレス (最低)
    if(who == 46) return l * 6 + 8;  // 7:ブレード・ダンサー (高い+)
    if(who == 47) return l * 2 + 5;  // 8:ハーモニスト (低い)
    if(who == 48) return l * 5 + 4;  // 9:ディスアレンジャー (高い+)
    // 2段階目進化 (10-14)
    if(who == 49) return l * 3 + 6;  // 10:ギア・ナイト (並)
    if(who == 50) return l * 1 + 2;  // 11:キャッスル・ウォール (最低)
    if(who == 51) return l * 7 + 12; // 12:サイクロン・ダンサー (高い++)
    if(who == 52) return l * 2 + 6;  // 13:コンダクター (低い)
    if(who == 53) return l * 6 + 6;  // 14:カオス・ジャマー (高い++)
    // 3段階目 (15-21)
    if(who == 54) return l * 2 + 7;  // 15:ヴァンガード (遅い)
    if(who == 55) return l * 7 + 10; // 16:スワッシュバックラー (速い)
    if(who == 56) return l * 1 + 2;  // 17:バスティオン
    if(who == 57) return l * 2 + 3;  // 18:イージス
    if(who == 58) return l * 9 + 15; // 19:テンペスト (最速)
    if(who == 59) return l * 3 + 7;  // 20:マエストロ
    if(who == 60) return l * 7 + 8;  // 21:ディスコード
    // 4段階目 (22-35)
    if(who == 61) return l * 3 + 8;   // 22:オーバーロード
    if(who == 62) return l * 2 + 7;   // 23:デストロイヤー
    if(who == 63) return l * 9 + 12;  // 24:ゼロ・ブレード
    if(who == 64) return l * 10 + 15; // 25:ヴォイド・ストーカー
    if(who == 65) return l * 1 + 2;   // 26:アダマンタイト
    if(who == 66) return l * 1 + 2;   // 27:インヴィンシブル
    if(who == 67) return l * 3 + 5;   // 28:ディヴァイン・シールド
    if(who == 68) return l * 2 + 4;   // 29:リジェネレーター
    if(who == 69) return l * 11 + 18; // 30:シルフィード
    if(who == 70) return l * 10 + 16; // 31:アクセラレーター
    if(who == 71) return l * 4 + 8;   // 32:アーク・ハーモニスト
    if(who == 72) return l * 6 + 10;  // 33:シンフォニア
    if(who == 73) return l * 8 + 10;  // 34:パンデモニウム
    if(who == 74) return l * 9 + 12;  // 35:ジョーカー
    // 特殊 (36-37)
    if(who == 75) return l * 100 + 500; // 36:はぐれノイズ (超素早さ)
    if(who == 76) return l * 120 + 600; // 37:ノイズ・キング (極素早さ)
    return 0;
  }
  int decide_Sense(int l, int who){
    if(who == 0) return l * 1 + 2;  // 0:ストライカー (最低)
    if(who == 1) return l * 1 + 2;  // 1:ガーディアン (最低)
    if(who == 2) return l * 2 + 3;  // 2:クリッパー (低い)
    if(who == 3) return l * 5 + 5;  // 3:メンダー (高い)
    if(who == 4) return l * 4 + 5;  // 4:ジャマー (高い)
    // 1段階目進化
    if(who == 5) return l * 1 + 2;  // 5:ギア・ソルジャー (最低)
    if(who == 6) return l * 1 + 2;  // 6:フォートレス (最低)
    if(who == 7) return l * 2 + 3;  // 7:ブレード・ダンサー (低い)
    if(who == 8) return l * 6 + 8;  // 8:ハーモニスト (高い+)
    if(who == 9) return l * 5 + 6;  // 9:ディスアレンジャー (高い+)
    // 2段階目進化 (10-14)
    if(who == 10) return l * 1 + 2;  // 10:ギア・ナイト (最低)
    if(who == 11) return l * 1 + 2;  // 11:キャッスル・ウォール (最低)
    if(who == 12) return l * 2 + 3;  // 12:サイクロン・ダンサー (低い)
    if(who == 13) return l * 7 + 12; // 13:コンダクター (高い++)
    if(who == 14) return l * 6 + 8;  // 14:カオス・ジャマー (高い++)
    // 3段階目 (15-21)
    if(who == 15) return l * 1 + 2;  // 15:ヴァンガード
    if(who == 16) return l * 3 + 5;  // 16:スワッシュバックラー
    if(who == 17) return l * 1 + 2;  // 17:バスティオン
    if(who == 18) return l * 5 + 10; // 18:イージス (支援)
    if(who == 19) return l * 2 + 3;  // 19:テンペスト
    if(who == 20) return l * 9 + 18; // 20:マエストロ (最高)
    if(who == 21) return l * 8 + 12; // 21:ディスコード
    // 4段階目 (22-35)
    if(who == 22) return l * 2 + 3;   // 22:オーバーロード
    if(who == 23) return l * 1 + 2;   // 23:デストロイヤー
    if(who == 24) return l * 4 + 6;   // 24:ゼロ・ブレード
    if(who == 25) return l * 3 + 5;   // 25:ヴォイド・ストーカー
    if(who == 26) return l * 1 + 2;   // 26:アダマンタイト
    if(who == 27) return l * 3 + 5;   // 27:インヴィンシブル
    if(who == 28) return l * 8 + 15;  // 28:ディヴァイン・シールド
    if(who == 29) return l * 9 + 18;  // 29:リジェネレーター
    if(who == 30) return l * 3 + 5;   // 30:シルフィード
    if(who == 31) return l * 2 + 4;   // 31:アクセラレーター
    if(who == 32) return l * 12 + 25; // 32:アーク・ハーモニスト
    if(who == 33) return l * 10 + 20; // 33:シンフォニア
    if(who == 34) return l * 11 + 20; // 34:パンデモニウム
    if(who == 35) return l * 9 + 15;  // 35:ジョーカー
    // 特殊 (36-37)
    if(who == 36) return l * 8 + 25; // 36:はぐれノイズ (旋律なし)
    if(who == 37) return l * 12 + 25; // 37:ノイズ・キング (旋律なし)

    //主人公
    if(who == 38) return l * 3 + 20;
    //仲間
    if(who == 39) return l * 1 + 2;  // 0:ストライカー (最低)
    if(who == 40) return l * 1 + 2;  // 1:ガーディアン (最低)
    if(who == 41) return l * 2 + 3;  // 2:クリッパー (低い)
    if(who == 42) return l * 5 + 5;  // 3:メンダー (高い)
    if(who == 43) return l * 4 + 5;  // 4:ジャマー (高い)
    // 1段階目進化
    if(who == 44) return l * 1 + 2;  // 5:ギア・ソルジャー (最低)
    if(who == 45) return l * 1 + 2;  // 6:フォートレス (最低)
    if(who == 46) return l * 2 + 3;  // 7:ブレード・ダンサー (低い)
    if(who == 47) return l * 6 + 8;  // 8:ハーモニスト (高い+)
    if(who == 48) return l * 5 + 6;  // 9:ディスアレンジャー (高い+)
    // 2段階目進化 (10-14)
    if(who == 49) return l * 1 + 2;  // 10:ギア・ナイト (最低)
    if(who == 50) return l * 1 + 2;  // 11:キャッスル・ウォール (最低)
    if(who == 51) return l * 2 + 3;  // 12:サイクロン・ダンサー (低い)
    if(who == 52) return l * 7 + 12; // 13:コンダクター (高い++)
    if(who == 53) return l * 6 + 8;  // 14:カオス・ジャマー (高い++)
    // 3段階目 (15-21)
    if(who == 54) return l * 1 + 2;  // 15:ヴァンガード
    if(who == 55) return l * 3 + 5;  // 16:スワッシュバックラー
    if(who == 56) return l * 1 + 2;  // 17:バスティオン
    if(who == 57) return l * 5 + 10; // 18:イージス (支援)
    if(who == 58) return l * 2 + 3;  // 19:テンペスト
    if(who == 59) return l * 9 + 18; // 20:マエストロ (最高)
    if(who == 60) return l * 8 + 12; // 21:ディスコード
    // 4段階目 (22-35)
    if(who == 61) return l * 2 + 3;   // 22:オーバーロード
    if(who == 62) return l * 1 + 2;   // 23:デストロイヤー
    if(who == 63) return l * 4 + 6;   // 24:ゼロ・ブレード
    if(who == 64) return l * 3 + 5;   // 25:ヴォイド・ストーカー
    if(who == 65) return l * 1 + 2;   // 26:アダマンタイト
    if(who == 66) return l * 3 + 5;   // 27:インヴィンシブル
    if(who == 67) return l * 8 + 15;  // 28:ディヴァイン・シールド
    if(who == 68) return l * 9 + 18;  // 29:リジェネレーター
    if(who == 69) return l * 3 + 5;   // 30:シルフィード
    if(who == 70) return l * 2 + 4;   // 31:アクセラレーター
    if(who == 71) return l * 12 + 25; // 32:アーク・ハーモニスト
    if(who == 72) return l * 10 + 20; // 33:シンフォニア
    if(who == 73) return l * 11 + 20; // 34:パンデモニウム
    if(who == 74) return l * 9 + 15;  // 35:ジョーカー
    // 特殊 (36-37)
    if(who == 75) return l * 8 + 25; // 36:はぐれノイズ (旋律なし)
    if(who == 76) return l * 12 + 25; // 37:ノイズ・キング (旋律なし)
    return 0;
  }
  int decide_Luck(int l, int who){
    if(who == 0) return l * 3 + 3;  // 0:ストライカー (並)
    if(who == 1) return l * 2 + 3;  // 1:ガーディアン (低い)
    if(who == 2) return l * 4 + 5;  // 2:クリッパー (高い)
    if(who == 3) return l * 3 + 3;  // 3:メンダー (並)
    if(who == 4) return l * 5 + 5;  // 4:ジャマー (高い)
    // 1段階目進化
    if(who == 5) return l * 3 + 3;  // 5:ギア・ソルジャー (並)
    if(who == 6) return l * 2 + 3;  // 6:フォートレス (低い)
    if(who == 7) return l * 5 + 6;  // 7:ブレード・ダンサー (高い+)
    if(who == 8) return l * 3 + 3;  // 8:ハーモニスト (並)
    if(who == 9) return l * 6 + 8;  // 9:ディスアレンジャー (高い+)
    // 2段階目進化 (10-14)
    if(who == 10) return l * 3 + 3;  // 10:ギア・ナイト (並)
    if(who == 11) return l * 2 + 3;  // 11:キャッスル・ウォール (低い)
    if(who == 12) return l * 6 + 8;  // 12:サイクロン・ダンサー (高い++)
    if(who == 13) return l * 3 + 3;  // 13:コンダクター (並)
    if(who == 14) return l * 7 + 12; // 14:カオス・ジャマー (高い++)
    // 3段階目 (15-21)
    if(who == 15) return l * 4 + 4;  // 15:ヴァンガード
    if(who == 16) return l * 7 + 10; // 16:スワッシュバックラー (クリティカル)
    if(who == 17) return l * 2 + 3;  // 17:バスティオン
    if(who == 18) return l * 4 + 5;  // 18:イージス
    if(who == 19) return l * 7 + 10; // 19:テンペスト
    if(who == 20) return l * 4 + 4;  // 20:マエストロ
    if(who == 21) return l * 9 + 15; // 21:ディスコード (最高)
    // 4段階目 (22-35)
    if(who == 22) return l * 5 + 5;   // 22:オーバーロード
    if(who == 23) return l * 4 + 4;   // 23:デストロイヤー
    if(who == 24) return l * 9 + 12;  // 24:ゼロ・ブレード
    if(who == 25) return l * 10 + 15; // 25:ヴォイド・ストーカー
    if(who == 26) return l * 2 + 3;   // 26:アダマンタイト
    if(who == 27) return l * 3 + 4;   // 27:インヴィンシブル
    if(who == 28) return l * 5 + 6;   // 28:ディヴァイン・シールド
    if(who == 29) return l * 4 + 5;   // 29:リジェネレーター
    if(who == 30) return l * 10 + 12; // 30:シルフィード
    if(who == 31) return l * 8 + 10;  // 31:アクセラレーター
    if(who == 32) return l * 5 + 5;   // 32:アーク・ハーモニスト
    if(who == 33) return l * 6 + 6;   // 33:シンフォニア
    if(who == 34) return l * 12 + 20; // 34:パンデモニウム
    if(who == 35) return l * 11 + 18; // 35:ジョーカー
    // 特殊 (36-37)
    if(who == 36) return l * 15 + 50; // 36:はぐれノイズ (高幸運)
    if(who == 37) return l * 20 + 60; // 37:ノイズ・キング (高幸運)

    //主人公
    if(who == 38) return l * 3 + 20;
    //仲間
    if(who == 39) return l * 3 + 3;  // 0:ストライカー (並)
    if(who == 40) return l * 2 + 3;  // 1:ガーディアン (低い)
    if(who == 41) return l * 4 + 5;  // 2:クリッパー (高い)
    if(who == 42) return l * 3 + 3;  // 3:メンダー (並)
    if(who == 43) return l * 5 + 5;  // 4:ジャマー (高い)
    // 1段階目進化
    if(who == 44) return l * 3 + 3;  // 5:ギア・ソルジャー (並)
    if(who == 45) return l * 2 + 3;  // 6:フォートレス (低い)
    if(who == 46) return l * 5 + 6;  // 7:ブレード・ダンサー (高い+)
    if(who == 47) return l * 3 + 3;  // 8:ハーモニスト (並)
    if(who == 48) return l * 6 + 8;  // 9:ディスアレンジャー (高い+)
    // 2段階目進化 (10-14)
    if(who == 49) return l * 3 + 3;  // 10:ギア・ナイト (並)
    if(who == 50) return l * 2 + 3;  // 11:キャッスル・ウォール (低い)
    if(who == 51) return l * 6 + 8;  // 12:サイクロン・ダンサー (高い++)
    if(who == 52) return l * 3 + 3;  // 13:コンダクター (並)
    if(who == 53) return l * 7 + 12; // 14:カオス・ジャマー (高い++)
    // 3段階目 (15-21)
    if(who == 54) return l * 4 + 4;  // 15:ヴァンガード
    if(who == 55) return l * 7 + 10; // 16:スワッシュバックラー (クリティカル)
    if(who == 56) return l * 2 + 3;  // 17:バスティオン
    if(who == 57) return l * 4 + 5;  // 18:イージス
    if(who == 58) return l * 7 + 10; // 19:テンペスト
    if(who == 59) return l * 4 + 4;  // 20:マエストロ
    if(who == 60) return l * 9 + 15; // 21:ディスコード (最高)
    // 4段階目 (22-35)
    if(who == 61) return l * 5 + 5;   // 22:オーバーロード
    if(who == 62) return l * 4 + 4;   // 23:デストロイヤー
    if(who == 63) return l * 9 + 12;  // 24:ゼロ・ブレード
    if(who == 64) return l * 10 + 15; // 25:ヴォイド・ストーカー
    if(who == 65) return l * 2 + 3;   // 26:アダマンタイト
    if(who == 66) return l * 3 + 4;   // 27:インヴィンシブル
    if(who == 67) return l * 5 + 6;   // 28:ディヴァイン・シールド
    if(who == 68) return l * 4 + 5;   // 29:リジェネレーター
    if(who == 69) return l * 10 + 12; // 30:シルフィード
    if(who == 70) return l * 8 + 10;  // 31:アクセラレーター
    if(who == 71) return l * 5 + 5;   // 32:アーク・ハーモニスト
    if(who == 72) return l * 6 + 6;   // 33:シンフォニア
    if(who == 73) return l * 12 + 20; // 34:パンデモニウム
    if(who == 74) return l * 11 + 18; // 35:ジョーカー
    // 特殊 (36-37)
    if(who == 75) return l * 15 + 50; // 36:はぐれノイズ (高幸運)
    if(who == 76) return l * 20 + 60; // 37:ノイズ・キング (高幸運)
    return 0;
  }
  void setBossStats(int hp, int tp, int atk, int def, int spd, int sen, int lck) {
    MaxHP = hp;
    HP = hp;
    originalMaxHP = hp;
    MaxTP = tp;
    TP = tp;
    Attack = atk;
    Defense = def;
    Speed = spd;
    Sense = sen;
    Luck = lck;
  }
  void forceLearnSkill(int skillId) {
    learnSkill(Skill(skillId));
  }
  Status(int level, int w){
    Level = level;
    who = w;
    MaxHP = decide_MaxHP(level, w);
    originalMaxHP = MaxHP;
    HP = MaxHP;
    //tune point
    MaxTP = decide_MaxTP(level, w);
    TP = MaxTP;
    //物理攻撃に関係
    Attack = decide_Attack(level, w);
    //防御に関係
    Defense = decide_Defense(level, w);
    //回避率、命中率に関係
    Speed = decide_Speed(level, w);
    //旋律、ノイズ攻撃に使用
    Sense = decide_Sense(level, w);
    // ドロ率、クリ率に関係
    Luck = decide_Luck(level, w);
    currentXP = 0;
    nextLevelXP = calculateNextXP(Level);
    learnedSkills.reserve(10);
    updateName();
    equipWeaponId = -1;
    equipArmorId = -1;
    equipAccId = -1;
    isDoubleAction = false;
    coverTurns = 0;
    physDamageOneTurns = 0;
    endureTurns = 0;
    counterTurns = 0;
    autoReviveTurns = 0;
    statusImmuneTurns = 0;
    attributeResistTurns = 0;
    cantMoveTurns = 0;
    reflectAllTurns = 0;
    damageGuardCount = 0;
    tauntTurns = 0;
    untargetableTurns = 0;
    poisonTurns = 0; paralyzedTurns = 0; silencedTurns = 0; confusedTurns = 0;
    atkBuffRate = 1.0; atkBuffTurns = 0; defBuffRate = 1.0; defBuffTurns = 0;
    spdBuffRate = 1.0; spdBuffTurns = 0; senBuffRate = 1.0; senBuffTurns = 0;
    lckBuffRate = 1.0; lckBuffTurns = 0; evaBuffRate = 1.0; evaBuffTurns = 0;
    atkDebuffRate = 1.0; atkDebuffTurns = 0; defDebuffRate = 1.0; defDebuffTurns = 0;
    spdDebuffRate = 1.0; spdDebuffTurns = 0; senDebuffRate = 1.0; senDebuffTurns = 0;
    lckDebuffRate = 1.0; lckDebuffTurns = 0;
    hpRegenTurns = 0; tpRegenTurns = 0; invalidDamageTurns = 0; 
    reflectPhysicalTurns = 0; reflectMagicTurns = 0;
    // ★★★ 初期技の習得を、テーブル参照方式に変更 ★★★
    checkLevelUpSkills(0, Level); // 0レベルから現在のレベルまで
  }

  void resetBattleStats() {
    MaxHP = originalMaxHP; // HP上限を戻す
    if (HP > MaxHP) HP = MaxHP;
    
    // バフ・デバフ・状態異常の全解除
    coverTurns = 0;
    physDamageOneTurns = 0;
    endureTurns = 0;
    counterTurns = 0;
    autoReviveTurns = 0;
    statusImmuneTurns = 0;
    attributeResistTurns = 0;
    cantMoveTurns = 0;
    reflectAllTurns = 0;
    damageGuardCount = 0;
    tauntTurns = 0;
    untargetableTurns = 0;
    poisonTurns = 0; paralyzedTurns = 0; silencedTurns = 0; confusedTurns = 0;
    atkBuffRate = 1.0; atkBuffTurns = 0; defBuffRate = 1.0; defBuffTurns = 0;
    spdBuffRate = 1.0; spdBuffTurns = 0; senBuffRate = 1.0; senBuffTurns = 0;
    lckBuffRate = 1.0; lckBuffTurns = 0; evaBuffRate = 1.0; evaBuffTurns = 0;
    atkDebuffRate = 1.0; atkDebuffTurns = 0; defDebuffRate = 1.0; defDebuffTurns = 0;
    spdDebuffRate = 1.0; spdDebuffTurns = 0; senDebuffRate = 1.0; senDebuffTurns = 0;
    lckDebuffRate = 1.0; lckDebuffTurns = 0;
    hpRegenTurns = 0; tpRegenTurns = 0; invalidDamageTurns = 0; 
    reflectPhysicalTurns = 0; reflectMagicTurns = 0;
    clearPopups();
  }
  // ★ MaxHP増加処理 (ID 62)
  void boostMaxHP() {
    if (MaxHP == originalMaxHP) { // 重ね掛け防止
      MaxHP = (int)(MaxHP * 1.5);
      HP = (int)(HP * 1.5); // 現在HPも割合で増やす
    }
  }

  int takedamage(int damage){
    // 1. ターン制無敵 (ID 63)
    if (invalidDamageTurns > 0) {
        return 0; // ダメージ0で終了 (回数は減らない)
    }
    // 2. 回数制バリア (ID 55, 64)
    if (damageGuardCount > 0) {
        damageGuardCount--; // ★ 1回消費
        return 0; // ダメージ0で終了
    }
    // 2. アダマン・ボディ (物理を1に)
    // (厳密には物理判定が必要だが、簡易的に全てのダメージを1にする)
    else if (physDamageOneTurns > 0) {
        if (damage > 1) damage = 1;
    }
    
    // 3. ラストスタンド (HP1で耐える)
    if (endureTurns > 0 && damage >= HP) {
        damage = HP - 1;
        endureTurns--; 
    }

    HP -= damage;
    if(HP < 0) HP = 0;
    
    return damage;
  }

  void ReceiveHeal(int amount) {
    if (HP <= 0) return; // 戦闘不能者は回復しない (蘇生は Revive を使う)
    
    HP += amount;
    if (HP > MaxHP) {
        HP = MaxHP;
    }
  }

  void Revive(int hpPercent) {
    if (HP > 0) return; // 既に生きている

    if (hpPercent <= 0) hpPercent = 1;
    if (hpPercent > 100) hpPercent = 100;
    
    // 最大HPの N% で復活
    HP = MaxHP * hpPercent / 100;
  }

  void CureStatus(bool cureDebuffs) {
    // 状態異常フラグをリセット
      poisonTurns = 0;
      poisonLevel = 0;
      paralyzedTurns = 0;
      silencedTurns = 0;
      confusedTurns = 0;

    // (例: スキルID 91 "リフレッシュ" の場合)
    if (cureDebuffs) {
        atkDebuffTurns = 0;
        defDebuffTurns = 0;
        spdDebuffTurns = 0;
    }
  }

  void ReceiveTP(int amount) {
    TP += amount;
    if (TP > MaxTP) {
        TP = MaxTP;
    }
    if (TP < 0) {
        TP = 0;
    }
  }

  void AddBuff(int skillId) {
    const int DEFAULT_BUFF_TURNS = 3;
    const int LONG_BUFF_TURNS = 5;

    switch (skillId) {
        // --- 主人公 ---
        case 7: // チューニング・アタック (単体 ATK)
            atkBuffRate = 1.5; atkBuffTurns = DEFAULT_BUFF_TURNS;
            break;
        case 8: // チューニング・ガード (単体 DEF)
            defBuffRate = 1.5; defBuffTurns = DEFAULT_BUFF_TURNS;
            break;
        case 9: // アレグロ (全体 SPD)
            spdBuffRate = 1.3; spdBuffTurns = DEFAULT_BUFF_TURNS;
            break;
        // --- ストライカー系 ---
        case 21: // パワーチャージ (ATK 1.5倍)
            atkBuffRate = 1.5; atkBuffTurns = DEFAULT_BUFF_TURNS;
            break;
        case 25: // ソードダンス (ATK/SPD 1.5倍)
            atkBuffRate = 1.5; atkBuffTurns = DEFAULT_BUFF_TURNS;
            spdBuffRate = 1.5; spdBuffTurns = DEFAULT_BUFF_TURNS;
            break;
        case 27:
            coverTurns = 1;
            break;
        case 29: // トリックステップ (SPD/LCK 1.5倍)
            spdBuffRate = 1.5; spdBuffTurns = DEFAULT_BUFF_TURNS;
            lckBuffRate = 1.5; lckBuffTurns = DEFAULT_BUFF_TURNS;
            break;
        case 31: // 王者の波動 (味方全体 ATK/DEF 1.5倍)
            atkBuffRate = 1.5; atkBuffTurns = DEFAULT_BUFF_TURNS;
            defBuffRate = 1.5; defBuffTurns = DEFAULT_BUFF_TURNS;
            break;
        case 32: // キングス・シールド (物理・旋律反射)
            reflectAllTurns = 1;
            break;
        case 34: // バーサーク (ATK 2倍 / DEF 0.5倍)
            atkBuffRate = 2.0; atkBuffTurns = LONG_BUFF_TURNS;
            defDebuffRate = 0.5; defDebuffTurns = LONG_BUFF_TURNS; // (※デバフも付く)
            break;
        case 39: // ミラーズエッジ (回避率 2倍)
            evaBuffRate = 2.0; evaBuffTurns = DEFAULT_BUFF_TURNS;
            break;
        case 43: // ダーククローク (姿を消す)
            untargetableTurns = DEFAULT_BUFF_TURNS;
            break;

        // --- ガーディアン系 ---
        case 46: // プロテクト (味方単体 DEF 1.5倍)
            defBuffRate = 1.5; defBuffTurns = DEFAULT_BUFF_TURNS;
            break;
        case 48: // ウォール (味方全体 DEF 1.2倍)
            defBuffRate = 1.2; defBuffTurns = DEFAULT_BUFF_TURNS;
            break;
        case 49: // 挑発
            tauntTurns = DEFAULT_BUFF_TURNS;
            break;
        case 50: // リフレクト (物理攻撃反射 1回)
            reflectPhysicalTurns = 1;
            break;
        case 51: // ガーディアン魂 (DEF 2倍、SPD 0.5倍)
            defBuffRate = 2.0; defBuffTurns = LONG_BUFF_TURNS;
            spdDebuffRate = 0.5; spdDebuffTurns = LONG_BUFF_TURNS; // (※デバフも付く)
            break;
        case 52: // 鉄壁 (DEF 2.5倍)
            defBuffRate = 2.5; defBuffTurns = DEFAULT_BUFF_TURNS;
            break;
        case 53: // カウンター
            counterTurns = DEFAULT_BUFF_TURNS;
            break;
        case 55: // フォースフィールド (ダメージ無効 1回)
            damageGuardCount = 1;
            break;
        case 56: // アダマン・ボディ (物理ダメージ 1)
            physDamageOneTurns = DEFAULT_BUFF_TURNS;
            break;
        case 57: // 自己修復 (HPリジェネ)
            hpRegenTurns = LONG_BUFF_TURNS;
            break;
        case 58: // ラストスタンド (HP1で耐える 1回)
            endureTurns = 1;
            break;
        case 59: // ギガンティック・ウォール (味方全体 DEF 2倍)
            defBuffRate = 2.0; defBuffTurns = DEFAULT_BUFF_TURNS;
            break;
        case 61: // オートリバイブ (自動蘇生 1回)
            autoReviveTurns = 99;
            break;
        case 62: // 最大HP上昇
            MaxHP = (int)(MaxHP * 1.5);
            HP = (int)(HP * 1.5);
            break;
        case 63: // 無敵 (1ターン ダメージ 0)
            invalidDamageTurns = 1; // (次の行動まで)
            break;
        case 64: // 全体バリア (ダメージ無効 1回)
            damageGuardCount = 1;
            break;
        case 65: // 旋律反射
            reflectMagicTurns = DEFAULT_BUFF_TURNS;
            break;
        case 67: // ホーリーウォール (属性耐性UP)
            attributeResistTurns = DEFAULT_BUFF_TURNS;
            // (特殊: 属性耐性フラグ)
            break;

        // --- リジェネレーター系 ---
        case 70: // TPリジェネ
            tpRegenTurns = LONG_BUFF_TURNS;
            break;

        // --- クリッパー系 ---
        case 73: // クイックステップ (自身 SPD 1.5倍)
            spdBuffRate = 1.5; spdBuffTurns = DEFAULT_BUFF_TURNS;
            break;
        case 75: // エアリアルダンス (自身 AGI 1.5倍)
            evaBuffRate = 1.5; evaBuffTurns = DEFAULT_BUFF_TURNS;
            break;
        case 77: // エアステップ (味方単体 SPD/AGI 1.5倍)
            spdBuffRate = 1.5; spdBuffTurns = DEFAULT_BUFF_TURNS;
            evaBuffRate = 1.5; evaBuffTurns = DEFAULT_BUFF_TURNS;
            break;
        case 79: // ラピッドムーブ (味方全体 SPD 1.5倍)
            spdBuffRate = 1.5; spdBuffTurns = DEFAULT_BUFF_TURNS;
            break;
        case 81: // ウインドウォール (味方全体 回避率UP 1.5倍)
            evaBuffRate = 1.5; evaBuffTurns = DEFAULT_BUFF_TURNS;
            break;
        case 83: // 精霊の舞 (自身 TPリジェネ)
            tpRegenTurns = LONG_BUFF_TURNS;
            break;
        case 85: // オーバークロック (自身 2回行動)
            twoActionsTurns = 1;
            isDoubleAction = true;
            break;
        case 86: // リミットブレイク (自身 ATK/SPD 最大)
            // 3ターンの間、攻撃と素早さを 4.0倍 (強烈なバフ) にする
            atkBuffRate = 4.0; 
            atkBuffTurns = 3;
            
            spdBuffRate = 4.0; 
            spdBuffTurns = 3;
            break;

        // --- メンダー系 ---
        case 95: // オートリペア (単体 HP自動回復)
            hpRegenTurns = LONG_BUFF_TURNS;
            break;
        case 97: // リジェネフィールド (全体 HP自動回復)
            hpRegenTurns = LONG_BUFF_TURNS;
            break;
        case 99: // ホーリー・ウォール (状態異常無効 1回)
            statusImmuneTurns = 1;
            break;
        case 102: // TPリジェネ
            tpRegenTurns = LONG_BUFF_TURNS;
            break;
        case 103: // オラクルフィールド (全体 TP徐々に回復)
            tpRegenTurns = LONG_BUFF_TURNS;
            break;

        default:
            break;
    }
  }
  bool checkDebuffHit(int baseChance, Status* user) {
    if (user == nullptr) return true; // ユーザー指定なしなら必中（自分への副作用など）
    
    // 基本確率 + (かけた人の運 - かけられた人の運)
    int chance = baseChance + (user->getLuck() - this->getLuck());
    
    // 最低保証5%、最大95% (完全に無効化したい場合は属性耐性などで処理)
    if (chance < 5) chance = 5;
    if (chance > 95) chance = 95;

    return (random(0, 100) < chance);
  }
  bool AddDebuff(int skillId, Status* user = nullptr) {
    if (statusImmuneTurns > 0) {
      statusImmuneTurns--; // 1回消費して防ぐ
      return false; // デバフを適用せずに終了
    }
    const int DEFAULT_DEBUFF_TURNS = 3;
    int baseChance = 100; // デフォルトは100%
    // --- 成功率の設定 ---
    switch (skillId) {
      // 毒系
      case 105: baseChance = 80; break; // ポイズン
      case 110: baseChance = 70; break; // デッドリーポイズン
      // 麻痺系
      case 45:  baseChance = 60; break; // ヴォイド・ショック
      case 47:  baseChance = 40; break; // シールドバッシュ(追加効果は低め)
      case 116: baseChance = 50; break; // ロックダウン
      // 精神系
      case 109: baseChance = 70; break; // サイレンス
      case 113: baseChance = 50; break; // カオスフィールド(混乱)
      case 122: baseChance = 50; break; // かく乱
      // ステータスダウン系
      case 10:  baseChance = 90; break; // ラレンタンド
      case 11:  baseChance = 90; break; // ノイズ・ジャミング
      case 24:  baseChance = 80; break; // アーマーブレイク
      case 87:  baseChance = 80; break; // タービュランス
      case 104: baseChance = 85; break; // スロウ
      case 106: baseChance = 85; break; // パワーダウン
      case 107: baseChance = 85; break; // ガードダウン
      case 108: baseChance = 80; break; // エリア・スロウ
      case 112: baseChance = 80; break; // エリア・ブレイク
      case 118: baseChance = 70; break; // ワールド・ダウン
      // 必中系
      case 101: baseChance = 999; break; // ディスペル(必中)
      case 117: baseChance = 999; break; // バニッシュ(必中)
      // 特殊
      case 114: baseChance = 40; break; // ディザスター(全体異常)
      default: baseChance = 100; break;
    }
    if (!checkDebuffHit(baseChance, user)) {
      return false; // ミス！
    }
    switch (skillId) {
      // --- 主人公 ---
      case 10: // ラレンタンド (単体 SPD)
        spdDebuffRate = 0.7; spdDebuffTurns = DEFAULT_DEBUFF_TURNS;
        break;
      case 11: // ノイズ・ジャミング (全体 ATK)
        atkDebuffRate = 0.8; atkDebuffTurns = DEFAULT_DEBUFF_TURNS;
        break;
      // --- ストライカー系 (バフの副作用) ---
      // (case 34 は AddBuff 側で defDebuffRate = 0.5 をセット)
      // --- ギア・ナイト ---
      case 24: // アーマーブレイク (防御 0.7倍)
        defDebuffRate = 0.7; defDebuffTurns = DEFAULT_DEBUFF_TURNS;
        break;

      // --- ヴォイド・ストーカー ---
      case 45: // ヴォイド・ショック (高確率で麻痺)
        paralyzedTurns = DEFAULT_DEBUFF_TURNS;
        break;

      // --- ガーディアン系 ---
      case 47: // シールドバッシュ (確率でスタン/麻痺)
        paralyzedTurns = 1;
        break;
        
      // --- ガーディアン系 (バフの副作用) ---
      // (case 51 は AddBuff 側で spdDebuffRate = 0.5 をセット)

      // --- アクセラレーター ---
      case 87: // タービュランス (全体 SPD 0.7倍)
        spdDebuffRate = 0.7; spdDebuffTurns = DEFAULT_DEBUFF_TURNS;
        break;

      // --- メンダー系 (敵の強化解除) ---
      case 101: // ディスペル (敵単体 強化解除)
        atkBuffTurns = 0; defBuffTurns = 0; spdBuffTurns = 0;
        senBuffTurns = 0; lckBuffTurns = 0; evaBuffTurns = 0;
        hpRegenTurns = 0; tpRegenTurns = 0;
        // (他の特殊バフもすべて解除)
        break;

      // --- ジャマー系 ---
      case 104: // スロウ (敵単体 SPD 0.7倍)
        spdDebuffRate = 0.7; spdDebuffTurns = DEFAULT_DEBUFF_TURNS;
        break;
      case 105: // ポイズン (毒)
        // 猛毒中なら通常毒で上書きしない
        if (poisonLevel < 2) {
            poisonLevel = 1;
            poisonTurns = DEFAULT_DEBUFF_TURNS;
        }
        break;
      case 106: // パワーダウン (敵単体 ATK 0.7倍)
        atkDebuffRate = 0.7; atkDebuffTurns = DEFAULT_DEBUFF_TURNS;
        break;
      case 107: // ガードダウン (敵単体 DEF 0.7倍)
        defDebuffRate = 0.7; defDebuffTurns = DEFAULT_DEBUFF_TURNS;
        break;
      case 108: // エリア・スロウ (敵全体 SPD 0.7倍)
        spdDebuffRate = 0.7; spdDebuffTurns = DEFAULT_DEBUFF_TURNS;
        break;
      case 109: // サイレンス (沈黙)
        silencedTurns = DEFAULT_DEBUFF_TURNS;
        break;
      case 110: // デッドリーポイズン (猛毒)
        poisonLevel = 2;
        poisonTurns = DEFAULT_DEBUFF_TURNS;
        break;
      case 112: // エリア・ブレイク (敵全体 ATK/DEF 0.7倍)
        atkDebuffRate = 0.7; atkDebuffTurns = DEFAULT_DEBUFF_TURNS;
        defDebuffRate = 0.7; defDebuffTurns = DEFAULT_DEBUFF_TURNS;
          break;
      case 113: // カオスフィールド (混乱)
        confusedTurns = DEFAULT_DEBUFF_TURNS;
        break;
      case 114: // ディザスター (全状態異常)
        if (poisonLevel < 2) {
            poisonLevel = 1;
            poisonTurns = DEFAULT_DEBUFF_TURNS;
        }
        paralyzedTurns = DEFAULT_DEBUFF_TURNS;
        silencedTurns = DEFAULT_DEBUFF_TURNS;
        confusedTurns = DEFAULT_DEBUFF_TURNS;
        break;
      case 116: // ロックダウン (行動不能/麻痺)
        paralyzedTurns = DEFAULT_DEBUFF_TURNS;
        break;
      case 117: // バニッシュ (敵単体 強化全解除)
        // (101:ディスペル と同じ効果)
        atkBuffTurns = 0; defBuffTurns = 0; spdBuffTurns = 0;
        senBuffTurns = 0; lckBuffTurns = 0; evaBuffTurns = 0;
        hpRegenTurns = 0; tpRegenTurns = 0;
        break;
      case 118: // ワールド・ダウン (敵全体 全能力 0.7倍)
        atkDebuffRate = 0.7; atkDebuffTurns = DEFAULT_DEBUFF_TURNS;
        defDebuffRate = 0.7; defDebuffTurns = DEFAULT_DEBUFF_TURNS;
        spdDebuffRate = 0.7; spdDebuffTurns = DEFAULT_DEBUFF_TURNS;
        senDebuffRate = 0.7; senDebuffTurns = DEFAULT_DEBUFF_TURNS;
        lckDebuffRate = 0.7; lckDebuffTurns = DEFAULT_DEBUFF_TURNS;
        break;

        // --- はぐれノイズ ---
      case 122: // かく乱 (混乱)
        confusedTurns = DEFAULT_DEBUFF_TURNS;
        break;

        default:
            break;
    }
    return true;
  }

  int calculateNextXP(int level) {
    return 10 + (level * level * 5);
  }

  void recalculateStats() {
    // 現在のHPが最大HPを超えるのを防ぐため、上昇分だけ加算する
    int oldMaxHP = MaxHP;
    MaxHP = decide_MaxHP(Level, who);
    originalMaxHP = MaxHP;
    HP += (MaxHP - oldMaxHP); // 上昇分を加算
    if (HP > MaxHP) HP = MaxHP; // (もし全回復させたいなら HP = MaxHP;)

    // TPや他のステータスは再計算
    MaxTP = decide_MaxTP(Level, who);
    TP = MaxTP; // TPは全回復
    Attack = decide_Attack(Level, who);
    Defense = decide_Defense(Level, who);
    Speed = decide_Speed(Level, who);
    Sense = decide_Sense(Level, who);
    Luck = decide_Luck(Level, who);
  }

  bool useTP(int cost) {
    if (TP >= cost) {
      TP -= cost;
      return true;
    }
    return false; // TPが足りない
  }

  int gainXP(int amount) {
    if (Level >= 99) return 0;

    currentXP += amount;
    bool leveledUp = false;
    int oldLevel = Level;

    while (currentXP >= nextLevelXP && Level < 99) {
      currentXP -= nextLevelXP; 
      Level++;
      nextLevelXP = calculateNextXP(Level);
      leveledUp = true;
    }

    if (leveledUp) {
      // ★ クラス内部なので、そのまま 'evolutionTable' を参照できる
      for (int i = 0; i < evolutionRuleCount; i++) {
        const EvolutionRule& rule = evolutionTable[i]; 

        if (rule.before_who_id == this->who &&
            rule.trigger_type == TRIGGER_LEVEL && // ★ 内部なので 'Status::' は不要
            this->Level >= rule.trigger_value) 
        {
          evolve(rule.after_who_id); 
          return 2; // 「進化した」
        }
      }
      recalculateStats();
      checkLevelUpSkills(oldLevel, Level);
      return 1; // 「レベルアップのみ」
    }
    return 0; // 変化なし
  }

  int caclatedamage(int Attack, int Defense, int ASpeed, int DSpeed, int ALuck, int DLuck, bool &retIsCrit){
    // 回避計算
    int baseHitRate = 95;
    int hitRate = baseHitRate + (ASpeed - DSpeed);
    if(hitRate > 100) hitRate = 100;
    else if(hitRate < 5) hitRate = 5;
    
    bool isHit = (random(0, 100) < hitRate);
    if(!isHit) {
        retIsCrit = false; // ミス
        return 0;
    }

    // クリ計算
    int basecriticalRate = 5;
    int criticalRate = basecriticalRate + (ALuck - DLuck);
    if(criticalRate > 100) criticalRate = 100;
    else if(criticalRate < 0) criticalRate = 0;
    
    // ★ 計算結果を引数の変数に書き込む
    retIsCrit = (random(0, 100) < criticalRate);

    // ダメージ計算 (前回修正した改良版の式)
    float effectiveDef = (float)Defense * 0.5;
    if (retIsCrit) effectiveDef *= 0.5; // 貫通

    int damage = (int)((float)Attack - effectiveDef);

    if (retIsCrit) damage = damage * 1.5; // 倍率

    float variance = (float)random(90, 111) / 100.0;
    damage = (int)((float)damage * variance);

    int minDamage = Attack / 20; 
    if (minDamage < 1) minDamage = 1;
    if (damage < minDamage) damage = minDamage;
    damage /= 4;
    return damage;
  }

  int caclulateSkillDamage(Status* target, Skill& skill, bool &retIsCrit) {
    // --- 0. 命中判定 (ここが抜けていました) ---
    // 回復・バフ・デバフ・蘇生・治療は必中とする
    // 攻撃系(DAMAGE, MULTI_HIT, SPECIAL)のみ判定を行う
    if (skill.type == Skill::EffectType::DAMAGE || 
        skill.type == Skill::EffectType::MULTI_HIT_DAMAGE ||
        skill.type == Skill::EffectType::SPECIAL) 
    {
        bool isSureHit = false;
        
        // ★★★ 必中スキルIDリスト ★★★
        // 38:ソニックブレイド, 80:インビジブルエッジ, 84:マッハブレイド, 121:ソニックダガー
        if (skill.id == 38 || skill.id == 80 || skill.id == 84 || skill.id == 121) {
            isSureHit = true;
        }
        // 魔法(旋律)攻撃も基本必中とするならここに追加(今回は物理と同じ扱いで計算)

        if (!isSureHit) {
            // 命中率 = 95 + (自分のSPD - 相手のSPD)
            int hitRate = 95 + (this->getSpeed() - target->getSpeed());
            
            // 上限・下限設定
            if(hitRate > 100) hitRate = 100;
            if(hitRate < 20) hitRate = 20; // 最低でも20%は当たるようにする

            // 判定
            if (random(0, 100) >= hitRate) {
                return 0; // ★ ミス！ (ダメージ0を返す)
            }
        }
    }
    if ((target->getWho() == 36 || target->getWho() == 37|| target->getWho() == 75 || target->getWho() == 76) && 
        skill.dependence == Skill::StatDependence::SEN) {
      retIsCrit = false;
      return 0; // ダメージ0 (無効)
    }
    // --- 基礎ステータス決定 ---
    int offensiveVal = (skill.dependence == Skill::StatDependence::SEN) ? this->getSense() : this->getAttack();
    int defensiveVal = (skill.dependence == Skill::StatDependence::SEN) ? target->getSense() : target->getDefense();

    // --- 特殊技の威力補正 ---
    float skillPower = (float)skill.power;

    // ID 35: カラミティ・エンド (HPが低いほど高威力)
    if (skill.id == 35) {
        float hpRatio = (float)this->getHp() / (float)this->getMaxHp();
        // HP100%なら1倍、HP1%なら3倍など
        skillPower = skillPower * (3.0 - (hpRatio * 2.0)); 
    }
    // ID 119: エナジー・バーン (敵のTPが多いほど高威力)
    else if (skill.id == 119) {
        skillPower += target->getTp() / 2; 
    }
    // ID 115: ペイン・イーター (状態異常の敵に威力2倍)
    else if (skill.id == 115) {
        if (target->getPoisonTurns() > 0 || target->getParalyzedTurns() > 0 || 
            target->getSilencedTurns() > 0 || target->getConfusedTurns() > 0) {
            skillPower *= 2.0;
        }
    }

    // --- 会心判定 ---
    int critBonus = 0;
    // ID 28, 40: 高クリティカル
    if (skill.id == 28 || skill.id == 40) critBonus = 30; 

    int critRate = 5 + (this->getLuck() - target->getLuck()) + critBonus;
    if(critRate > 100) critRate = 100;
    if(critRate < 0) critRate = 0;
    retIsCrit = (random(0, 100) < critRate);

    // --- 防御力計算 ---
    float effectiveDef = (float)defensiveVal / 2.0;

    // ID 24, 124: 防御無視 (アーマーブレイク, キングスピア)
    if (skill.id == 24 || skill.id == 124) {
        effectiveDef = 0;
    }
    // 会心時は貫通
    else if (retIsCrit) {
        effectiveDef *= 0.5; 
    }

    // --- 最終ダメージ計算 ---
    // (power 50 を基準倍率 1.0 とする)
    float powerMultiplier = skillPower / 50.0;
    int baseDamage = (int)((float)offensiveVal * powerMultiplier);
    
    int damage = baseDamage - (int)effectiveDef;
    if (target->isDefending) {
      damage = (int)(damage * 0.7);
    }
    if (target->attributeResistTurns > 0) {
      damage = damage / 4;
    }
    // 会心ボーナス (1.5倍)
    if (retIsCrit) damage = damage * 1.5;

    // 乱数
    float variance = (float)random(90, 111) / 100.0;
    damage = (int)((float)damage * variance);
    damage /= 4;
    // 最低保証
    int minDamage = offensiveVal / 20;
    if (minDamage < 1) minDamage = 1;
    if (damage < minDamage) damage = minDamage;

    return damage;
  }

  // ★★★ 3. その他の特殊処理 ★★★
  void limitBreak() { // ID 86
      // バフを最大ターン・最大倍率で付与 (簡易実装)
      atkBuffRate = 3.0; atkBuffTurns = 3;
      spdBuffRate = 3.0; spdBuffTurns = 3;
  }

  // ★★★ 修正: 引数に bool &retIsCrit を追加 ★★★
  int calculateHealAmount(Skill& skill, bool &retIsCrit) {
    int base = this->getSense();
    float multiplier = (float)skill.power / 50.0;
    int heal = (int)((float)base * multiplier);
    
    // --- ★ 会心判定 (回復) ---
    // (回復の会心率は運の10%程度とする)
    int critRate = this->getLuck() / 10; 
    if (critRate < 5) critRate = 5; // 最低5%
    
    retIsCrit = (random(0, 100) < critRate);

    if (retIsCrit) heal = heal * 2.0; // 会心なら1.5倍回復
    // ------------------------
    
    float variance = (float)random(90, 111) / 100.0;
    heal = (int)((float)heal * variance);
    
    if (heal < 1) heal = 1;
    heal /= 4;
    return heal;
  }

  bool isPlayer() {
    return (who >= 38 && who <= 79); // GDDのID定義 (38以上は味方)
  }

  void addAttack(int amount) {
    Attack += amount;
    // (将来的に上限なども設定)
  }
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
void loop() {
  ctx->memMonitor.update();
  if (ctx->requestRegenerate) {
    ctx->requestRegenerate = false;

    // MapとHeroの内容だけ再初期化（new/deleteなし）
    noInterrupts();
    ctx->map->regenerate(20, 20, Map::TYPE_DUNGEON);
    ctx->hero->reset(*ctx->map);

    ctx->graphic->setFloor(ctx->map->currentFloor);

    int cameraX = ctx->hero->X - Graphic::SCREEN_WIDTH / 2;
    int cameraY = ctx->hero->Y - Graphic::SCREEN_HEIGHT / 2;
    ctx->graphic->invalidateAndRedraw(*ctx->map, *ctx->hero, cameraX, cameraY);
    interrupts();
  }
  static GameState prevState = STATE_GAME;
  static int gameOverCursor = 0;
  auto& g = *ctx->graphic;
  auto& map = *ctx->map;
  auto& hero = *ctx->hero;
  auto& ctrl = *ctx->controller;
  auto& menu = *ctx->menu;
  auto& encounter = *ctx->encounter;
  auto& inventory = *ctx->inventory;
  auto& party = *ctx->party;
  auto& state = ctx->state;
  auto& music = *ctx->music;
  auto& sd = *ctx->sd;
  auto& currentEvent = ctx->currentEvent;
  auto& save = *ctx->saveManager;
  auto& vib = *ctx->vibration;
  auto& imgmgr = *ctx->imgMgr;
  auto& conf = ctx->config;
  vib.update();
  if (state == STATE_GAME) {
    hero.oldX = hero.X;
    hero.oldY = hero.Y;

    int prevX = hero.X, prevY = hero.Y;
    ctrl.update_cara_point(hero);
    if (ctrl.pressed(ctrl.BTN_UP))    hero.direction = Caractor::DIR_UP;
    if (ctrl.pressed(ctrl.BTN_DOWN))  hero.direction = Caractor::DIR_DOWN;
    if (ctrl.pressed(ctrl.BTN_LEFT))  hero.direction = Caractor::DIR_LEFT;
    if (ctrl.pressed(ctrl.BTN_RIGHT)) hero.direction = Caractor::DIR_RIGHT;
    ctrl.check_wall(hero, map);

    bool eventOccurred = false;
    if (ctrl.pressedDebounced(ctrl.BTN_A)){
      eventOccurred = ctrl.check_event(hero, map, state, currentEvent);
    }
    // 2. 移動が発生したかチェック
    bool moved = (hero.X != prevX || hero.Y != prevY);
    // 3. 移動していて、メニューが開いていない場合のみイベントとエンカウントをチェック
    if (moved && !menu.active) {
      // 5. イベントが発生しなかった場合のみ、エンカウントをチェック
      if (!eventOccurred && !map.isTown) {
        if (!map.isTown && map.currentType != Map::MapType::TYPE_BOSS_ROOM && encounter.checkEncounter()) {
          vib.trigger(300);
          state = STATE_BATTLE;
          ctx->battle->start(music, sd, hero, party, map.currentFloor, imgmgr, map);
        }
      }
    }

    // 置換箇所（STATE_GAME 内）
    int cameraX = hero.X - Graphic::SCREEN_WIDTH / 2;
    int cameraY = hero.Y - Graphic::SCREEN_HEIGHT / 2;
    // map が再生成されたときは drawFullBackground を呼んでいるので通常は smartRender だけでOK
    g.smartRender(map, hero, cameraX, cameraY);


    if (ctrl.pressed(ctrl.BTN_X)) {
      menu.toggle();
      if (menu.active) state = STATE_MENU;
    }
  }

  else if (state == STATE_MENU) {
    //menu.update(ctrl, inventory, hero, party);
    menu.update(ctrl, inventory, hero, party, map, music, sd, save, conf, vib, ctx->bossDefeated);
    //g.screenSprite.fillScreen(TFT_BLACK);
    menu.draw(&g, inventory, hero, party, conf);
    //g.screenSprite.pushSprite(0,0);

    if (!menu.active) {
      state = STATE_GAME; // ゲーム画面に戻る
      //もしうまくいかなかったらここを
      ctx->requestRegenerate = false;
    }
  }

  else if (state == STATE_BATTLE) {
    auto &battle = *ctx->battle;
    battle.update(ctrl, state, music, sd, hero, inventory, vib, map, g, ctx->bossDefeated);
    battle.draw(&g);
    //g.screenSprite.pushSprite(0, 0);
  }

  else if (state == STATE_EVENT) {
    
    // ★★★ ここから修正 ★★★
    
    // イベントの種類に応じて処理を分岐
    switch (currentEvent) {
      
      case EVENT_TREASURE_BOX: {
        // --- 宝箱イベント ---
          
          // 2a. プレイヤーの現在地を取得
        int heroTileX = (hero.X + Map::TILE_SIZE / 2) / Map::TILE_SIZE;
        int heroTileY = (hero.Y + Map::TILE_SIZE / 2) / Map::TILE_SIZE;

        // 2b. マップデータを「開いた」状態に更新
        map.mapData[heroTileY * map.getMAP_WIDTH() + heroTileX] = Map::TILE_BOX_OPEN;
          
        // 2. 中身の抽選
        int floor = map.currentFloor;
        int itemId = 0;
        int r = random(100);

        // --- 確率設定 ---
        // 45%: 消費道具
        // 30%: 素材
        // 15%: レア素材
        // 3%:  旋律の巻物
        // 7%:  装備品 (武器/防具/アクセ) ★ NEW!

        if (r < 45) { // 消費道具
          if (floor <= 10) itemId = 100;      // リペアキット
          else if (floor <= 30) itemId = 103; // エネルギー缶
          else itemId = 101;                  // リペアキット中
        } 
        else if (r < 75) { // 素材
          itemId = 2; // 銅の歯車
        }
        else if (r < 90) { // レア素材
          if (floor <= 20) itemId = 1; // 鉄くず(進化素材)
          else if (floor <= 30) itemId = 10 + random(0, 2); // 銀/金の歯車
          else itemId = 13; // 謎のパーツ
        }
        else if (r < 93) { // 巻物 (3%)
          int minSkill = 1, maxSkill = 5;
          if (floor > 10) { minSkill=6; maxSkill=11; }
          if (floor > 30) { minSkill=12; maxSkill=13; }
          itemId = 200 + random(minSkill, maxSkill + 1);
        }
        else { // ★★★ 装備品 (7%) ★★★
          int tier = (floor - 1) / 10; // 0～4
          if (tier > 4) tier = 4;
          
          // 装備カテゴリ抽選 (0:武器, 1:防具, 2:アクセ)
          int typeR = random(0, 3); 
          
          // ★ 激レア判定 (さらに10%の確率で最強装備)
          bool isRare = (random(100) < 10);

          if (typeR == 0) { // 武器
            if (isRare && floor >= 30) itemId = 399; // 創世のタクト
            else itemId = 300 + tier; // 階層に応じた武器
          } 
          else if (typeR == 1) { // 防具
            if (isRare && floor >= 30) itemId = 499; // イージス・ギア
            else itemId = 400 + tier; 
          } 
          else { // アクセ
            if (isRare && floor >= 30) itemId = 599; // トリニティ・コア
            else itemId = 500 + random(0, 5); // 500-504からランダム
          }
        }

        // 3. アイテム入手
        Item foundItem = createItemById(itemId);
        inventory.addItem(foundItem);
        
        // (メッセージ表示などは描画システムの都合上省略、あるいはフラグを立てて別途表示)
          
        // 2d. 即座にゲームに戻る (待機処理は行わない)
        state = STATE_GAME;
        currentEvent = EVENT_NONE; // イベントタイプをリセット
        break; // EVENT_TREASURE_BOX 終了
      }
      case EVENT_STAIR_UP: {
        map.currentFloor++;
        int width = 0, height = 0;
        Map::MapType nextType = Map::MapType::TYPE_DUNGEON;
        if (map.currentFloor % 10 == 0){
          int bossIndex = (map.currentFloor / 10) - 1;
          // ボスを倒しているかチェック
          width = height = 5;
          if (ctx->bossDefeated[bossIndex]) {
            nextType = Map::MapType::TYPE_TOWN; // 倒してれば集落
            map.isTown = true;
            music.switchTrack(0, sd);  // 集落BGM
          } else {
            map.isTown = false;
            nextType = Map::MapType::TYPE_BOSS_ROOM; // まだならボス部屋
            music.switchTrack(1, sd); // ボス部屋BGM (ダンジョンと同じか、無音で緊張感を出す)
          }
        }else {
          // 通常階
          map.isTown = false;
          width = height = 20;
          nextType = Map::MapType::TYPE_DUNGEON;
          music.switchTrack(1, sd); // ダンジョンBGM
        }
        ctx->graphic->setFloor(map.currentFloor);
        ctx->map->regenerate(width, height, nextType);
        ctx->hero->reset(*ctx->map);
        state = STATE_GAME;
        currentEvent = EVENT_NONE;
        break;
      }
      case EVENT_STAIR_DOWN: {
        if (map.currentFloor > 1) {
          int width = 0, height = 0;
          map.currentFloor--;
          Map::MapType nextType = Map::MapType::TYPE_DUNGEON;
          if (map.currentFloor == 1) {
            nextType = Map::MapType::TYPE_TOWN;
            music.switchTrack(0, sd);
          }else if (map.currentFloor % 10 == 0) {
            width = height = 5;
            int bossIndex = (map.currentFloor / 10) - 1;
            if (ctx->bossDefeated[bossIndex]) {
              nextType = Map::MapType::TYPE_TOWN;
              music.switchTrack(0, sd);
              map.isTown = true;
            }else {
              // (ありえないが) ボス未撃破ならボス部屋
              nextType = Map::MapType::TYPE_BOSS_ROOM;
              music.switchTrack(1, sd);
            }
          }else {
            width = height = 20;
            // 通常階
            map.isTown = false;
            nextType = Map::MapType::TYPE_DUNGEON;
            music.switchTrack(1, sd);
          }
          // 3. マップ生成
          ctx->graphic->setFloor(map.currentFloor);
          ctx->map->regenerate(width, height, nextType);
          ctx->hero->reset(*ctx->map);
        }
        state = STATE_GAME;
        currentEvent = EVENT_NONE;
        break;
      }
      case EVENT_AUTOMATON: {
        // TODO: 「壊れたオートマタがある。調律しますか？」の
        // メッセージウィンドウを本当は出すべき

        // (今はAボタンで即座に仲間になる)
        // (Aボタンは check_event の呼び出し元で押されている)

        // TODO: 今は who=39 (初号機) で固定。
        // 将来はフロア番号やマップの保持データから who ID を決定する
        int who_to_add = map.automatonWhoId;
        Automaton* newAlly = new Automaton(1, who_to_add); // 主人公と同じレベルで加入
        
        int result = party.addMember(newAlly);
        
        if (result == 1) {
            // パーティーに入った
        } else if (result == 2) {
            // 預かり所へ送られた (自動)
        }
        
        // タイルを消す
        int heroTileX = (hero.X + Map::TILE_SIZE / 2) / Map::TILE_SIZE;
        int heroTileY = (hero.Y + Map::TILE_SIZE / 2) / Map::TILE_SIZE;
        map.mapData[heroTileY * map.getMAP_WIDTH() + heroTileX] = Map::TILE_GRASS;
        
        state = STATE_GAME;
        currentEvent = EVENT_NONE;
        break;
      }
      case EVENT_INN: {
        ctx->menu->active = true;
        ctx->menu->currentMenuState = Menu::STATE_INN;
        ctx->menu->listCursor = 0; // 0:はい, 1:いいえ
        state = STATE_MENU; // ゲーム画面からメニュー画面へ
        currentEvent = EVENT_NONE; // イベントフラグは解除してOK
        break;
      }
      // --- 預かり所 ---
      case EVENT_STORAGE: {
        // メニューの預かり所モードを起動
        menu.active = true;
        menu.currentMenuState = Menu::STATE_STORAGE;
        menu.storageMode = 0;
        menu.listCursor = 0;
        
        state = STATE_MENU; // メニュー画面へ
        currentEvent = EVENT_NONE;
        break;
      }
      // --- ショップ (後回し、とりあえずダミー) ---
      case EVENT_SHOP: {
        ctx->menu->active = true;
        ctx->menu->currentMenuState = Menu::STATE_SHOP_CHOICE;
        ctx->menu->listCursor = 0; // 0:買う, 1:売る, 2:出る
        state = STATE_MENU; 
        currentEvent = EVENT_NONE;
        break;
      }
      case EVENT_BOSS_BATTLE: {
        vib.trigger(500); // 警告振動
        state = STATE_BATTLE;
        
        // ボスBGM (階層に応じて変えるならここでID指定)
        // 10F=ID3, 50F=ID4 など
        // startの中で判定しているので、ここではそのまま呼ぶ
        ctx->battle->start(music, sd, hero, party, map.currentFloor, imgmgr, map);
        
        currentEvent = EVENT_NONE;
        break;
      }
      case EVENT_NONE:
      default:
        // 何らかのバグでイベントタイプが未設定の場合
        state = STATE_GAME; // とりあえずゲームに戻る
        break;
    }
    // ★★★ 修正ここまで ★★★
  }

  else if (state == STATE_GAME_OVER) {
    // -------------------------------------------------
    // 1. 入力処理 (描画ループの外に出す)
    // -------------------------------------------------
    // 描画中にボタン判定をすると重くなるので、必ずループの外で行います
    if (ctrl.pressedDebounced(ctrl.BTN_A)) {
      ctx->music->playSE(0); 
      // リセット
      rp2040.reboot();
      while (1) {
        // 何もしないで死を待つ
      }
      return;
    }

    // -------------------------------------------------
    // 2. 描画処理 (ラインスプライト方式)
    // -------------------------------------------------
    // 画面上部(0)から下部(SCREEN_HEIGHT)まで、ブロック単位でループ
    for (int drawY = 0; drawY < Graphic::SCREEN_HEIGHT; drawY += Graphic::BLOCK_HEIGHT) {
      
      // (1) スプライトをクリア
      ctx->graphic->lineSprite.fillScreen(TFT_BLACK);

      // (2) 文字描画設定
      // 左上(Top-Left)を基準点にします。これがないと位置がずれることがあります。
      ctx->graphic->lineSprite.setTextDatum(TL_DATUM); 

      // (3) "GAME OVER" 描画
      ctx->graphic->lineSprite.setTextColor(TFT_RED);
      ctx->graphic->lineSprite.setTextSize(3);
      // print ではなく drawString を使います
      // Y座標: 「本来のY座標(80) - 現在の描画開始位置(drawY)」
      ctx->graphic->lineSprite.drawString("GAME OVER", 60, 80 - drawY);

      // (4) "タイトルへ" 描画
      ctx->graphic->lineSprite.setTextSize(2);
      ctx->graphic->lineSprite.setTextColor(TFT_YELLOW);
      // Y座標: 「本来のY座標(150) - 現在の描画開始位置(drawY)」
      ctx->graphic->lineSprite.drawString("タイトルへ", 80, 150 - drawY);

      // (5) 画面への転送
      // 作った短冊を、画面上の drawY の位置に貼り付けます
      ctx->graphic->lineSprite.pushSprite(0, drawY);
    }
  }

  if (prevState != state) {
    if (state == STATE_GAME) {
      // メニュー／戦闘等からゲーム画面に戻った：背景を一括再描画してヒーローを正常復帰
      int cameraX = hero.X - Graphic::SCREEN_WIDTH / 2;
      int cameraY = hero.Y - Graphic::SCREEN_HEIGHT / 2;
      g.invalidateAndRedraw(map, hero, cameraX, cameraY);
    } else {
      // メニュー／戦闘へ入るときは「画面を上書きする」ので
      // prevHero を無効化して、restore が誤動作しないようにする
      g.prevHeroScreenX = -1;
      g.prevHeroScreenY = -1;
    }
    prevState = state;
  }
}
